drfailov/DRM_Watch_v3/Board/KiCad Project/_DRM_Watch_v3/2023-12-12.jpg

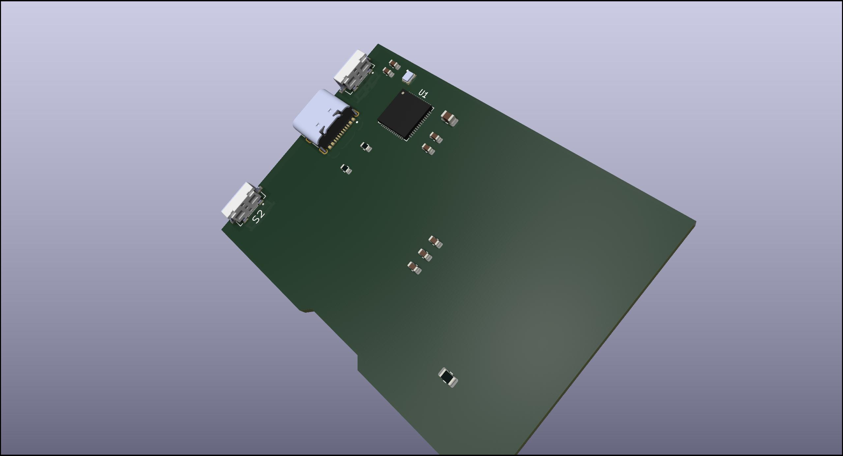
Board/KiCad Project/_DRM_Watch_v3/2023-12-12.jpg
