drfailov/DRM_Watch_v3/Board/KiCad Project/HV816K6 EL Driver/datasheet.png

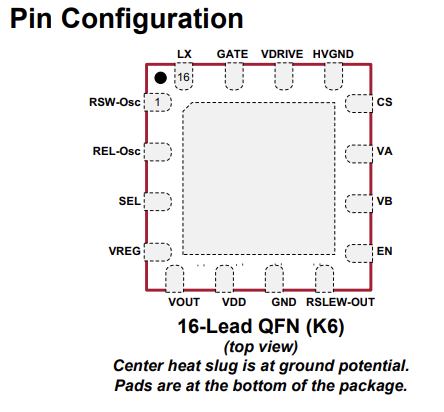
Board/KiCad Project/HV816K6 EL Driver/datasheet.png
