drfailov/DRM_Watch_v3/Board/KiCad Project/HV816K6 EL Driver/footprint.png

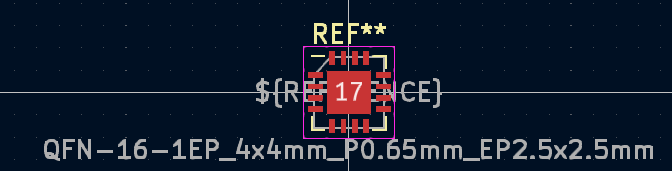
Board/KiCad Project/HV816K6 EL Driver/footprint.png
