drfailov/DRM_Watch_v3/Board/KiCad Project/HV816K6 EL Driver/symbol.png

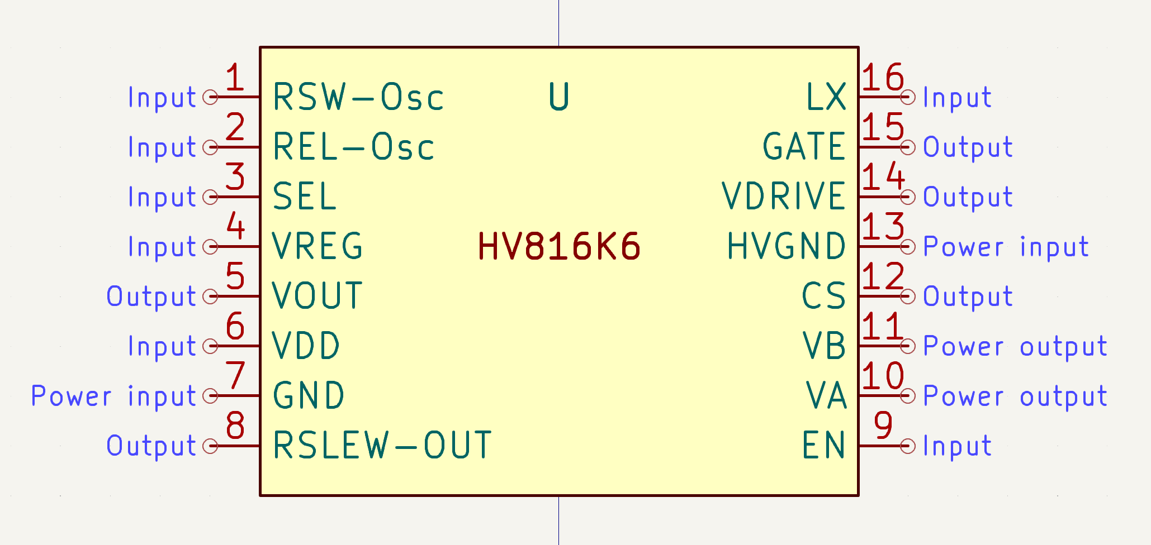
Board/KiCad Project/HV816K6 EL Driver/symbol.png
