drfailov/DRM_Watch_v3/Board/Photos/2023-12-20-1.png

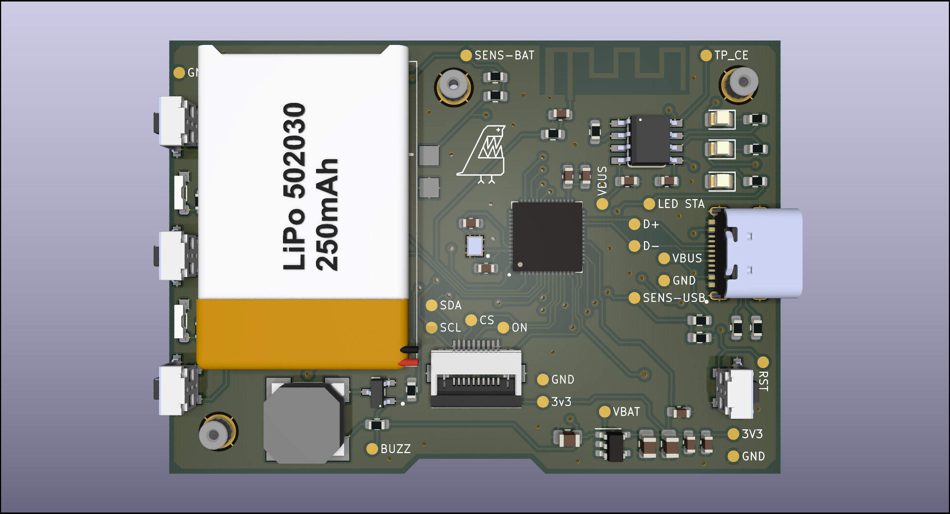
Board/Photos/2023-12-20-1.png
