drfailov/DRM_Watch_v3/Board/Photos/photo_2023-12-13_23-19-55.jpg

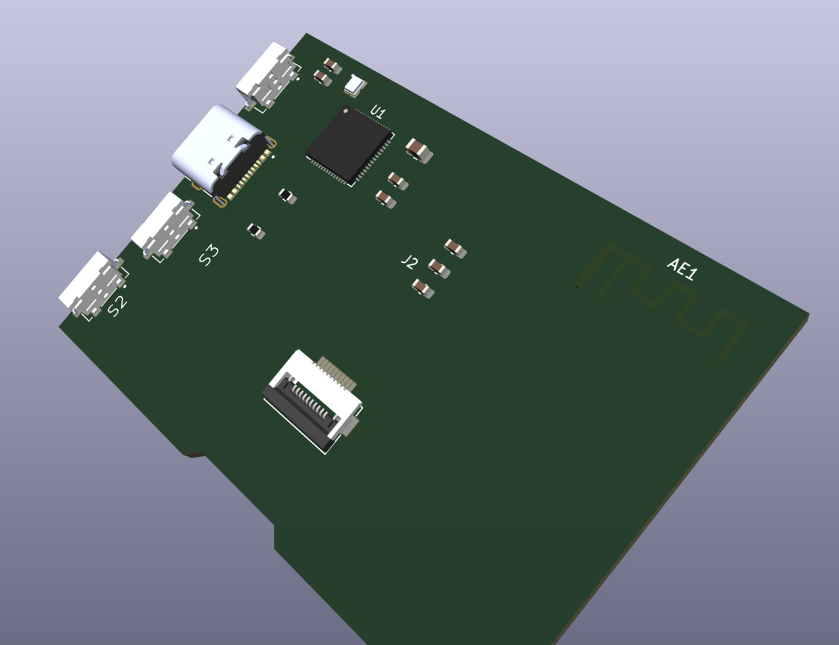
Board/Photos/photo_2023-12-13_23-19-55.jpg
