drfailov/DRM_Watch_v3/Board/Photos/photo_2023-12-15_01-00-38.jpg

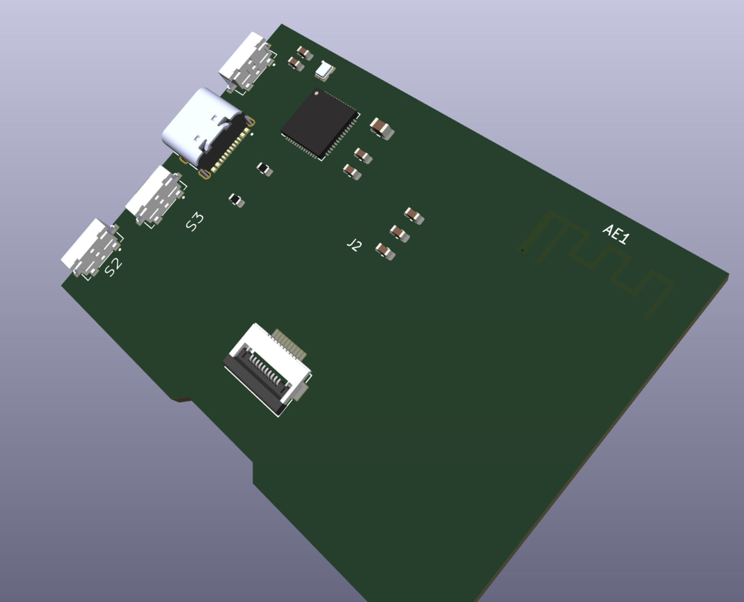
Board/Photos/photo_2023-12-15_01-00-38.jpg
