drfailov/DRM_Watch_v3/Board/Photos/photo_2023-12-16_00-13-19.jpg

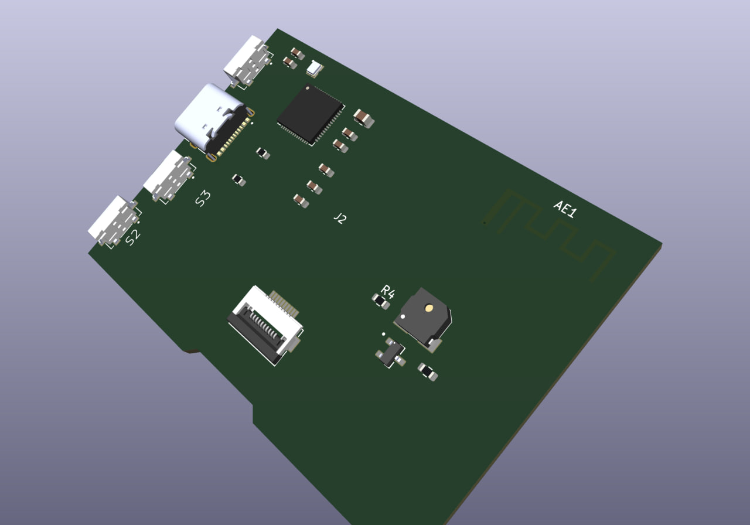
Board/Photos/photo_2023-12-16_00-13-19.jpg
