drfailov/DRM_Watch_v3/Board/Photos/photo_2023-12-16_18-21-03.jpg

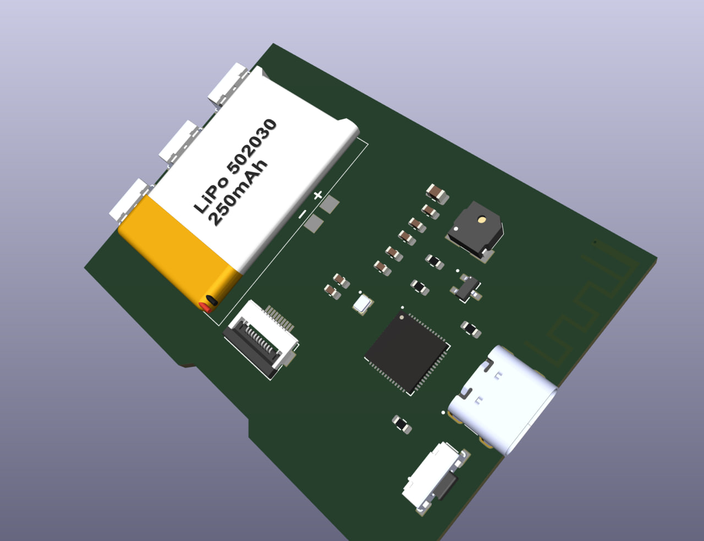
Board/Photos/photo_2023-12-16_18-21-03.jpg
