drfailov/DRM_Watch_v3/Board/Photos/photo_2023-12-16_20-18-11.jpg

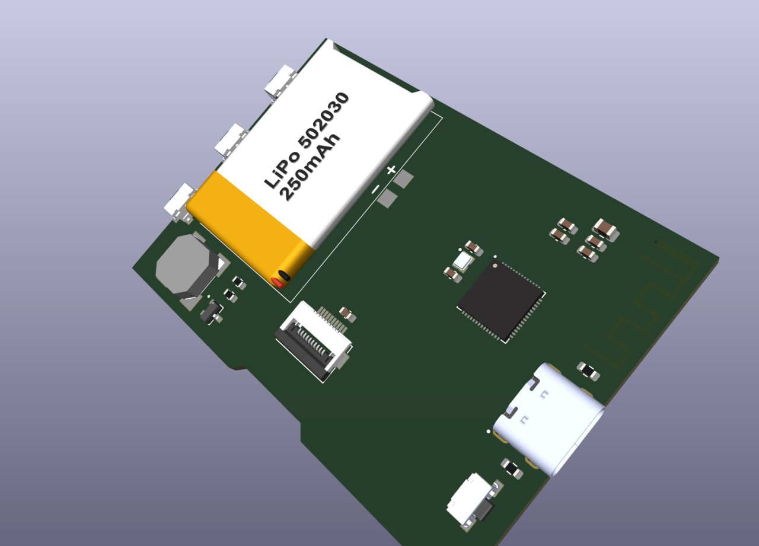
Board/Photos/photo_2023-12-16_20-18-11.jpg
