drfailov/DRM_Watch_v3/Board/Photos/photo_2023-12-17_21-03-23.jpg

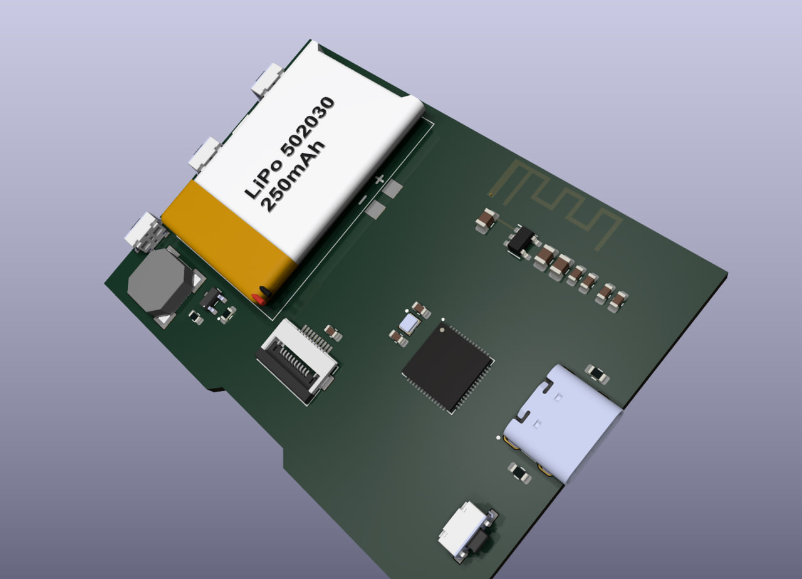
Board/Photos/photo_2023-12-17_21-03-23.jpg
