drfailov/DRM_Watch_v3/Board/Photos/photo_2023-12-18_10-02-20.jpg

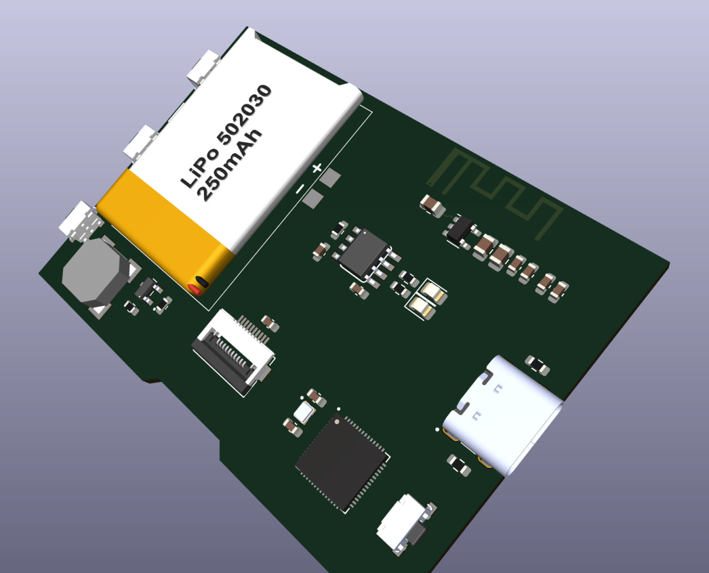
Board/Photos/photo_2023-12-18_10-02-20.jpg
