drfailov/DRM_Watch_v3/Board/Photos/photo_2023-12-18_23-56-38.jpg

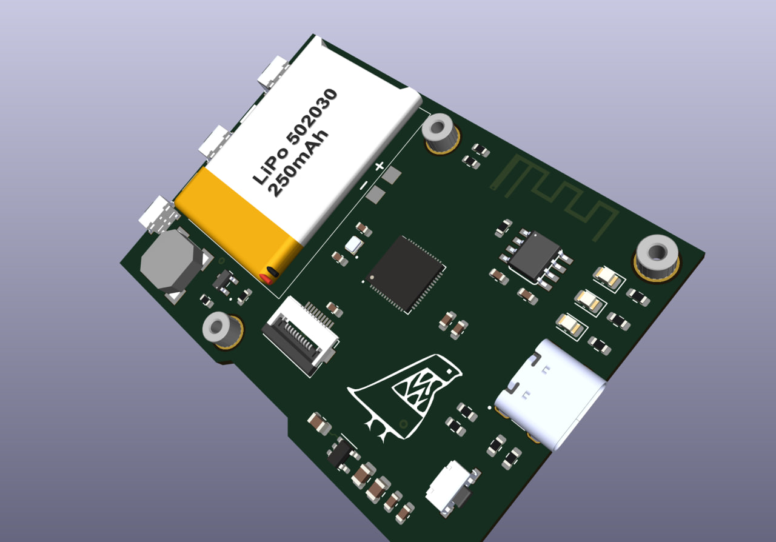
Board/Photos/photo_2023-12-18_23-56-38.jpg
