drfailov/DRM_Watch_v3/Board/Photos/photo_2023-12-20_00-25-11.jpg

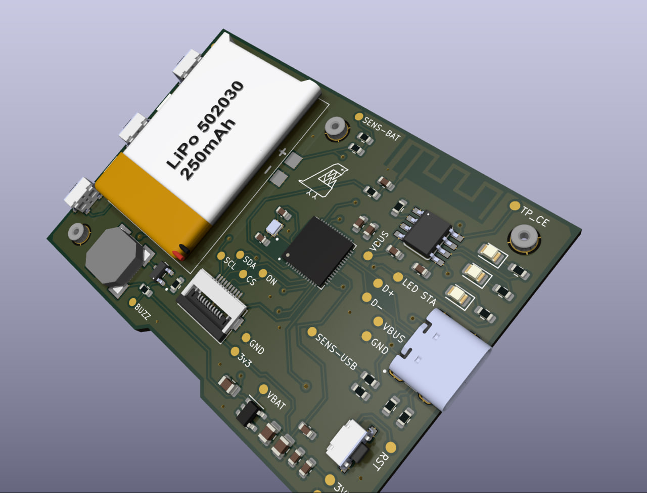
Board/Photos/photo_2023-12-20_00-25-11.jpg
