drfailov/DRM_Watch_v3/Case/2024-04-05 Back Cover Engraving.png

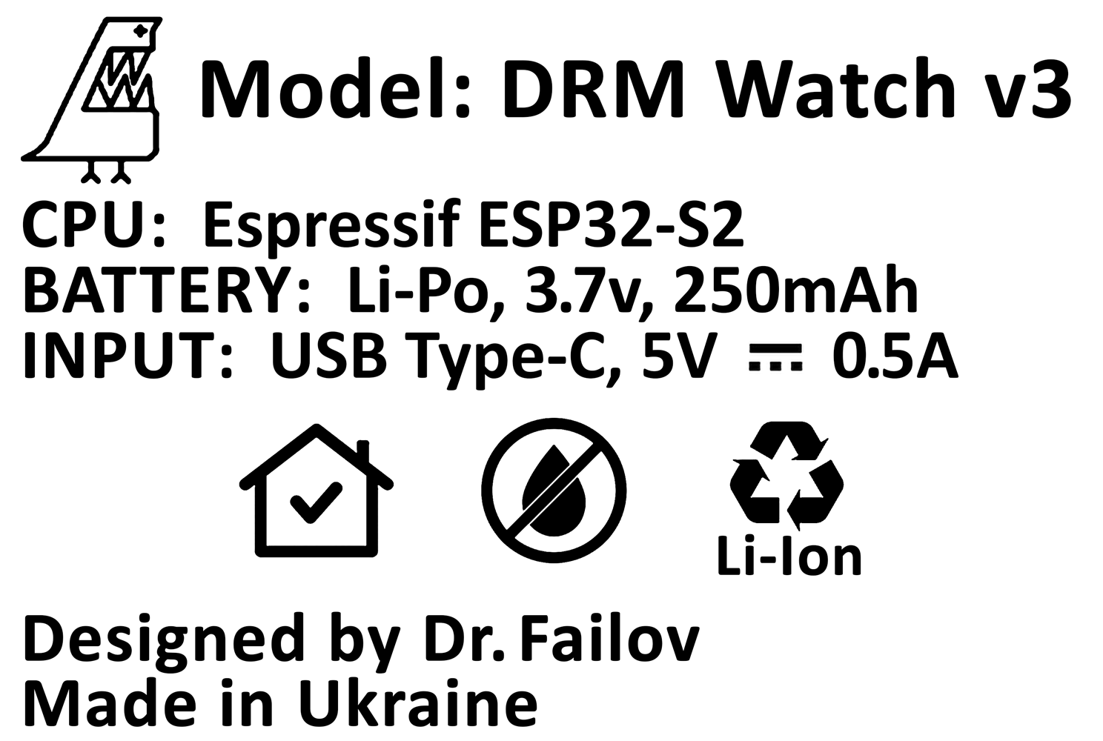
Case/2024-04-05 Back Cover Engraving.png
