drfailov/DRM_Watch_v3/Case/2024-04-16 Front Cover Engraving.png

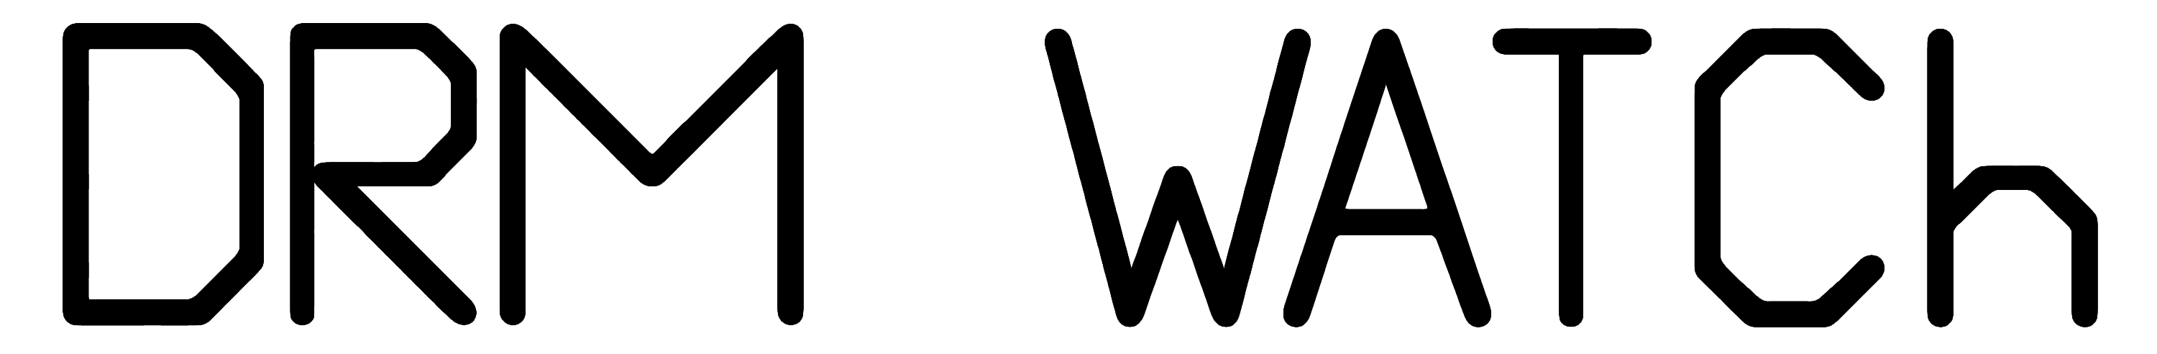
Case/2024-04-16 Front Cover Engraving.png
