drfailov/DRM_Watch_v3/Docs/s2_mini_v1.0.0_4_16x9.jpg

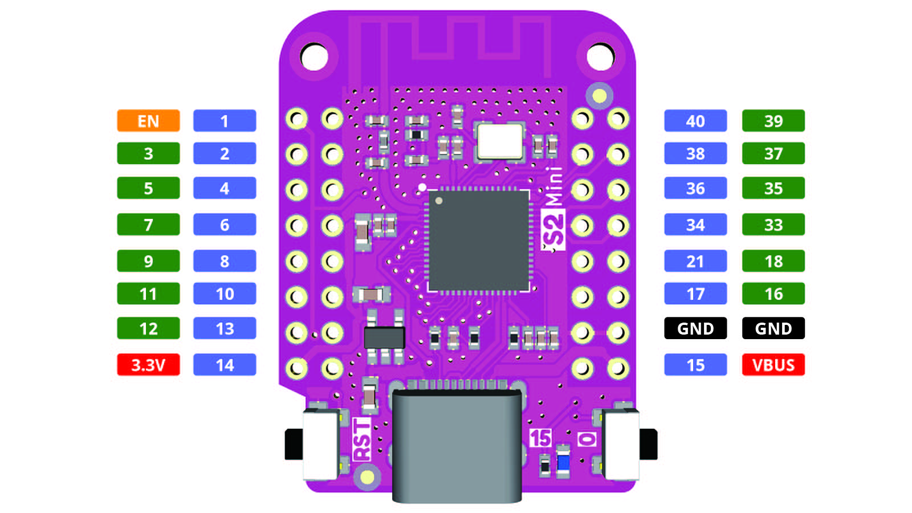
Docs/s2_mini_v1.0.0_4_16x9.jpg
