drfailov/DRM_Watch_v3/Docs/Screenshot 2023-10-04 231237.png

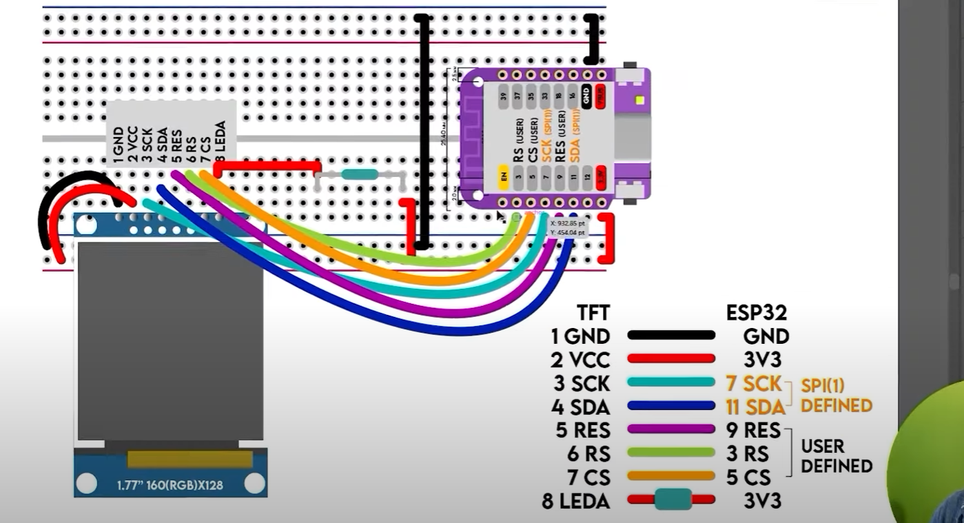
Docs/Screenshot 2023-10-04 231237.png
