drfailov/DRM_Watch_v3/Docs/Screenshot 2024-01-14 173355.png

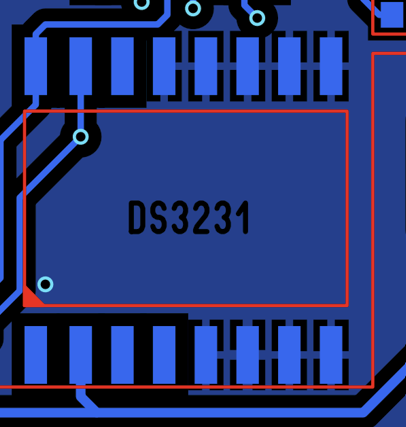
Docs/Screenshot 2024-01-14 173355.png
