drfailov/DRM_Watch_v3/ExampleFiles/capy-Masha.bmp

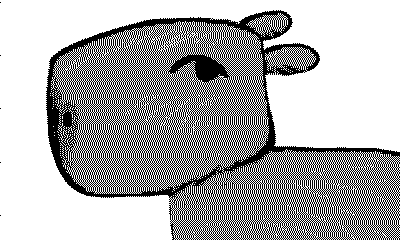
ExampleFiles/capy-Masha.bmp
