drfailov/DRM_Watch_v3/ExampleFiles/capy.bmp

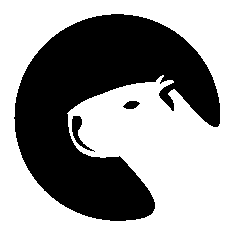
ExampleFiles/capy.bmp
