drfailov/DRM_Watch_v3/ExampleFiles/catGrisha.bmp

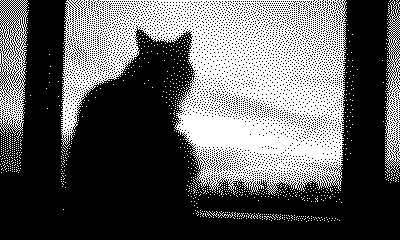
ExampleFiles/catGrisha.bmp
