drfailov/DRM_Watch_v3/ExampleFiles/DRM-Capy-v2.bmp

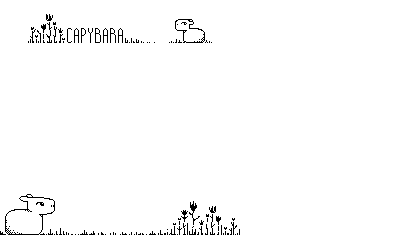
ExampleFiles/DRM-Capy-v2.bmp
