drfailov/DRM_Watch_v3/ExampleFiles/jessy.bmp

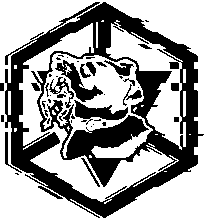
ExampleFiles/jessy.bmp
