drfailov/DRM_Watch_v3/ExampleFiles/mask1.bmp

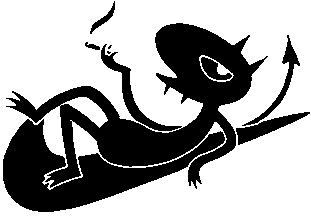
ExampleFiles/mask1.bmp
