drfailov/DRM_Watch_v3/ExampleFiles/mavic.bmp

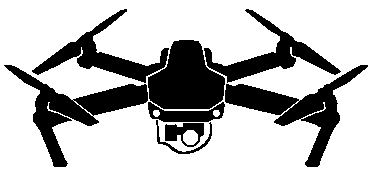
ExampleFiles/mavic.bmp
