drfailov/DRM_Watch_v3/ExampleFiles/Плата.bmp

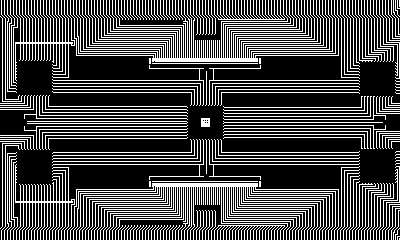
ExampleFiles/Плата.bmp
