drfailov/DRM_Watch_v3/Software/Flasher/esptool-gui/20240626_113028.jpg

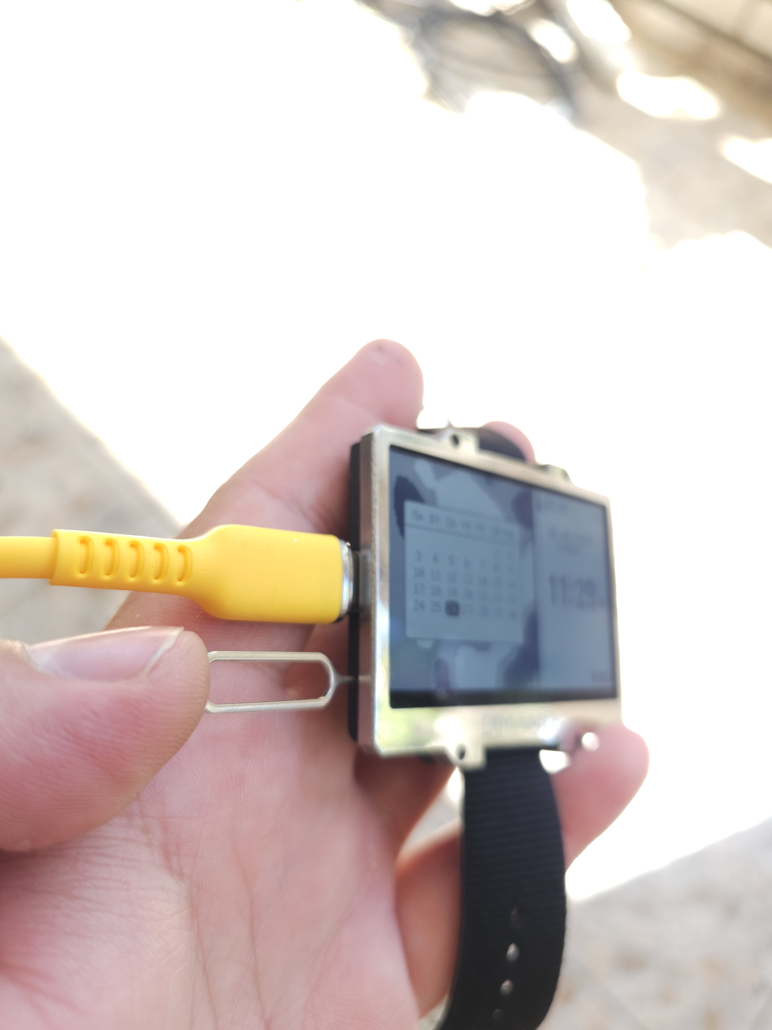
Software/Flasher/esptool-gui/20240626_113028.jpg
