drfailov/DRM_Watch_v3/Software/Flasher/esptool-gui/BootMode.png

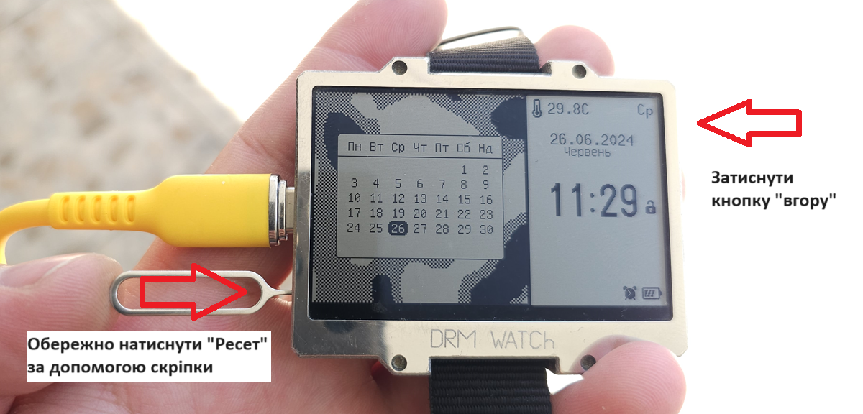
Software/Flasher/esptool-gui/BootMode.png
