drfailov/DRM_Watch_v3/Software/MIDI-to-Arduino-main/preview.jpg

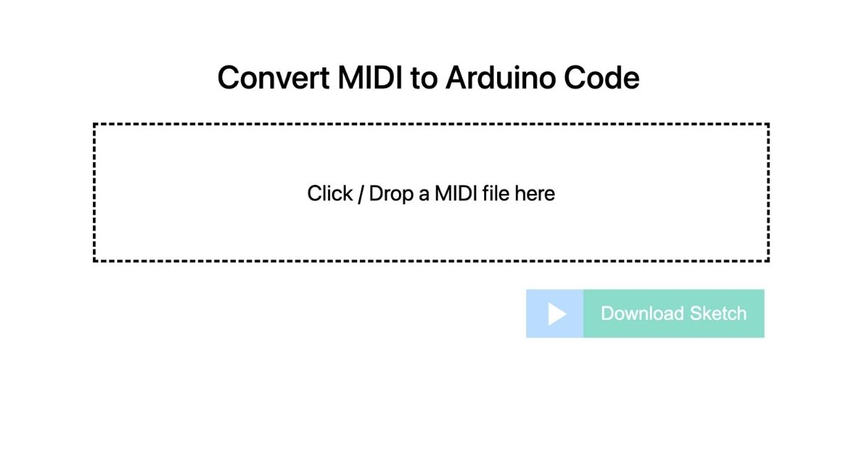
Software/MIDI-to-Arduino-main/preview.jpg
