drfailov/DRM_Watch_v3/Software/ScreenshotTool/loading-314p.gif

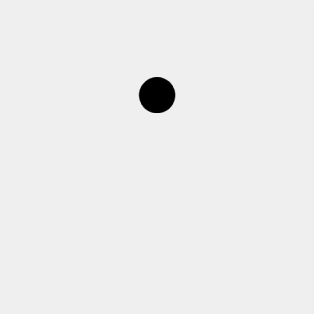
Software/ScreenshotTool/loading-314p.gif
