drfailov/DRM_Watch_v3/Software/ScreenshotTool/screenshot.png

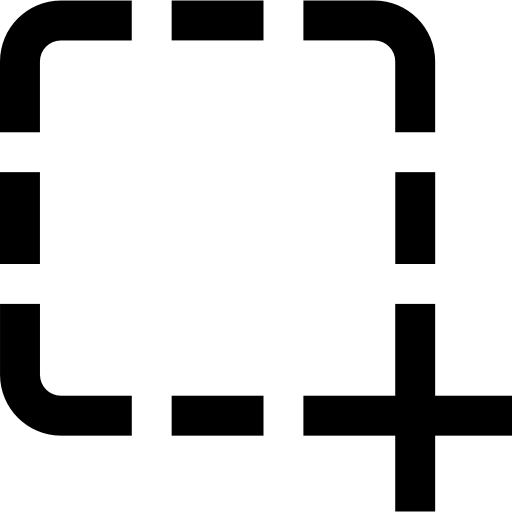
Software/ScreenshotTool/screenshot.png
