drfailov/DRM_Watch_v3/Software/ScreenshotTool/screenshot_tool/Resources/boot-mode-connected.png

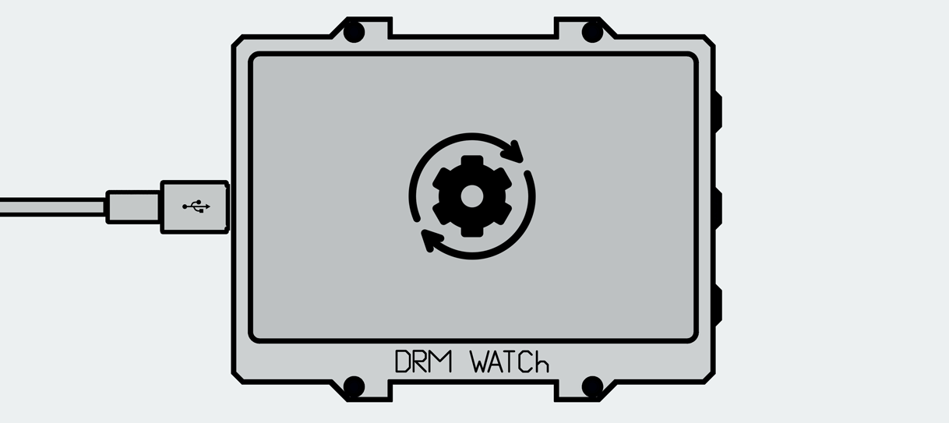
Software/ScreenshotTool/screenshot_tool/Resources/boot-mode-connected.png
