drfailov/DRM_Watch_v3/Case/2024-04-17 v200 front-case-engraving.dxf

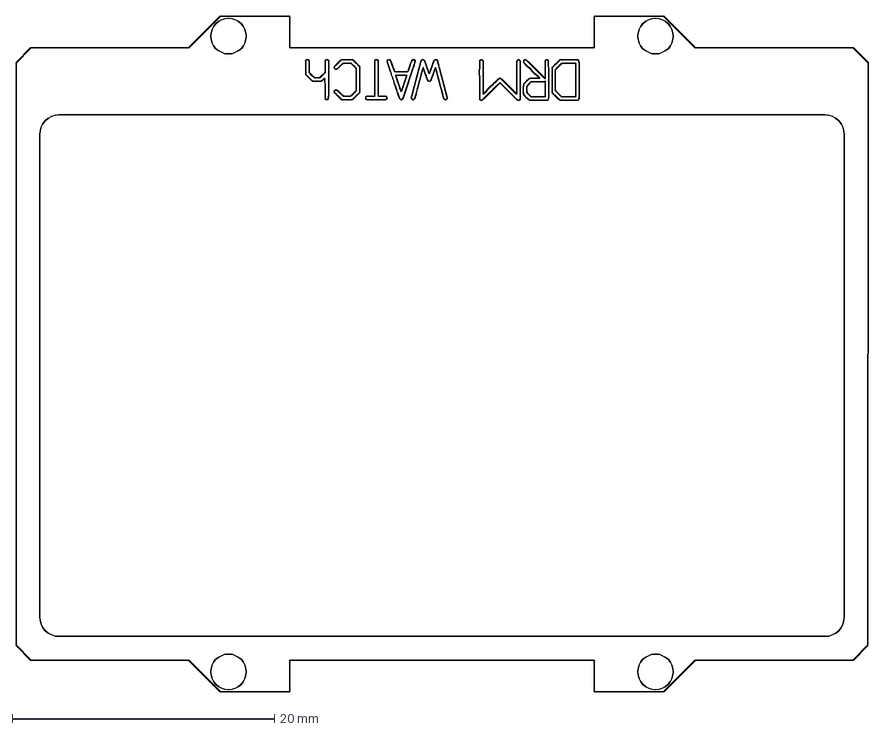
[picture p143: CAD file, 2024-04-18]
Case/2024-04-17 v200 front-case-engraving.dxf
64.9 x 51.4 mm
