drfailov/DRM_Watch_v3/Case/2024-04-17 v200 front-case.step

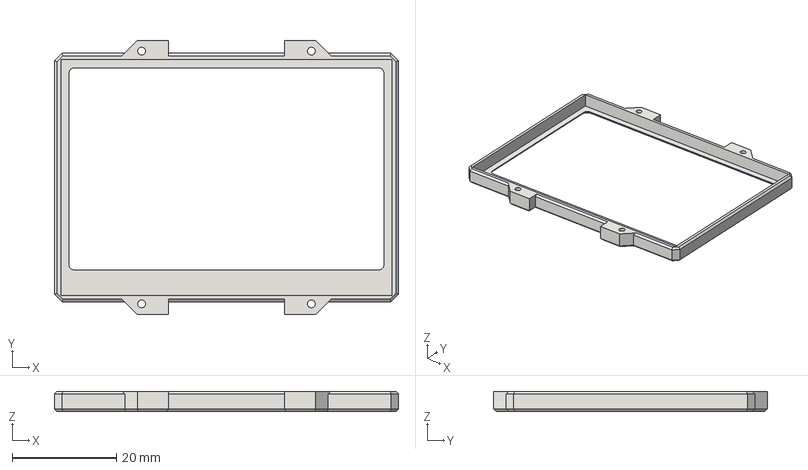
[picture p144: CAD file, 2024-04-18]
Case/2024-04-17 v200 front-case.step
65.9 x 52.4 x 3.90 mm
