drfailov/DRM_Watch_v3/Case/2024-04-17 v200 newbuttons.stl

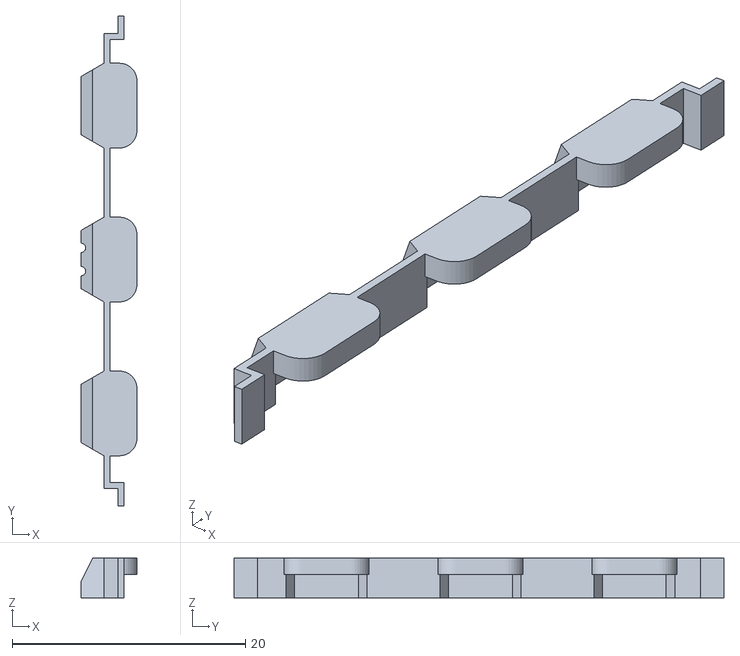
[picture p145: CAD file, 2024-04-17]
Case/2024-04-17 v200 newbuttons.stl
4.80 x 42.0 x 3.40
