drfailov/DRM_Watch_v3/Case/2024-04-05 Back Cover Engraving.dxf

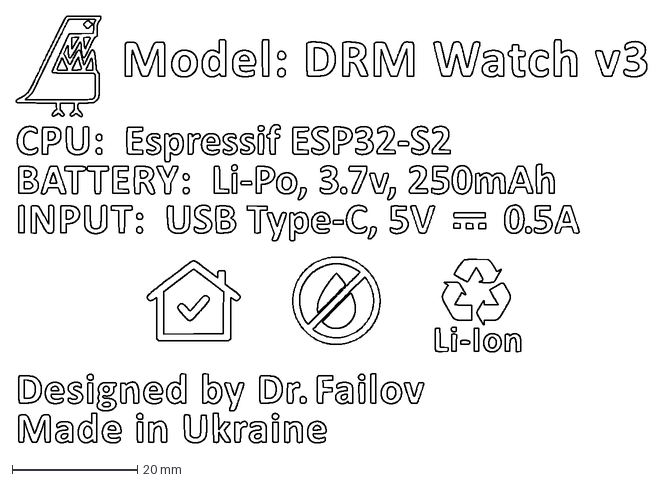
[picture p146: CAD file, 2024-04-06]
Case/2024-04-05 Back Cover Engraving.dxf
100.7 x 68.1 mm
