drfailov/DRM_Watch_v3/Firmware/DRM Watch 3/src/DrmPreferences.h

#ifndef MYYPREFERENCES_H
#define MYYPREFERENCES_H

#define LANG_UA 0
#define LANG_EN 1

/*PROTOTYPES*/
int getPreferencesFreeSpace();
// BATTERY
#define batteryCalibrationLengthMax 100 // 100 is one record for 5 minutes = 8 hours total
int16_t batteryCalibration[batteryCalibrationLengthMax];  //values written from higher[0] battery level to lower[batteryCalibrationLengthMax] battery level. 0 considered as end of data.
bool batteryCalibrationLoaded = false;
float batteryCalibrationGetValuePercent(int raw);
int batteryCalibrationGetIndexOfValue(int raw);
bool isBatteryCalibrated();
int batteryCalibrationLength();
int batteryCalibrationAddValue(int16_t raw);
void batteryCalibrationShrink();
void saveBatteryCalibration();
void resetBatteryCalibration();
void loadBatteryCalibration();
unsigned long getBatteryCalibrationValueAddInterval();
void saveBatteryCalibrationValueAddInterval(unsigned long value);
// SHORTCUTS
int getActionId(int eventId, int defaultActionId);
int getActionId(int eventId);
bool saveActionId(int eventId, int actionId);
int getActionArgument(int eventId);
bool saveActionArgument(int eventId, int value);
String getActionArgumentString(int eventId);
bool saveActionArgumentString(int eventId, String value);
// timer
bool saveTimerStartedTime(unsigned long epoch);
bool saveTimerTime(unsigned long epoch);
unsigned long getTimerStartedTime();
unsigned long getTimerTime();
bool isTimerRunning();
// lcd
bool getInversionValue();
bool getWhiteValue();
bool getBlackValue();
void saveLangValue(int value);
int getLang();
void saveInversionValue(bool value);
void saveEnterAnimationValue(bool value);
bool getEnterAnimationValue();
void saveClearAnimationValue(int value);
int getClearAnimation();
unsigned long getLcdSpiSpeed();
bool saveLcdSpiSpeed(unsigned long spiSpeed);
void saveRoundness(int value);
int getRoundness();
int getRoundness(int max);
// sound
bool getMuteEnabled();
bool saveMuteEnabled(bool value);
int getButtonSound();
bool saveButtonSound(int value);
bool saveSoundCoef(float coef);
float getSoundCoef();
// SAVED WI-FI
int wifiSlotCnt();
String wifiSlotName(int slot);
bool wifiSlotIsEmpty(int slot);
String wifiSlotPassword(int slot);
int getWifiSavedIndex(String name);
bool wifiSlotSave(int slot, String ssid, String password);
bool wifiSlotClear(int slot);
// alert
int getAlertsNumber();
bool getAlertEnabled(int index);
bool saveAlertEnabled(int index, bool value);
bool getAnyAlertEnabled();
int getAlertLastRunDay(int index);
bool saveAlertLastRunDay(int index, int value);
int getAlertHour(int index);
bool saveAlertHour(int index, int value);
int getAlertMinute(int index);
bool saveAlertMinute(int index, int value);
int getAlertMelody(int index);
bool saveAlertMelody(int index, int value);
String getAlertName(int index);
bool saveAlertName(int index, String newname);
// timesync
unsigned long getLastTimeSync();
bool saveLastTimeSync(unsigned long epoch);
bool getTimeSyncEnabled();
bool saveTimeSyncEnabled(bool value);
long getTimeOffsetSec();
bool saveTimeOffsetSec(long value);
bool saveLastChargedTime();
bool saveLastChargedTime(unsigned long epoch);
unsigned long getTimeSinceLastCharged();
unsigned long getLastTryTimeSync();
bool saveLastTryTimeSync(unsigned long epoch);
// stopwatch
bool saveStopwatchStartedTime(unsigned long epoch);
bool saveStopwatchFinishedTime(unsigned long epoch);
unsigned long getStopwatchStartedTime();
unsigned long getStopwatchFinishedTime();
bool isStopwatchRunning();
int stopwatchHistorySlotCnt();
unsigned long stopwatchHistorySlotStart(int slot);
bool stopwatchHistorySlotIsEmpty(int slot);
unsigned long stopwatchHistorySlotEnd(int slot);
bool saveStopwatchHistorySlotStart(int slot, unsigned long epoch);
bool saveStopwatchHistorySlotEnd(int slot, unsigned long epoch);
// watchface
int getWatchface();
bool saveWatchface(int value);
bool getWatchfaceStatusbarEnabled();
bool saveWatchfaceStatusbarEnabled(bool value);
bool getWatchfaceAnalogEnabled();
bool saveWatchfaceAnalogEnabled(bool value);
bool getWatchfaceDigitalEnabled();
bool saveWatchfaceDigitalEnabled(bool value);
bool getWatchfaceStatusbarDigitalEnabled();
bool saveWatchfaceStatusbarDigitalEnabled(bool value);
bool getWatchfaceTemperatureEnabled();
bool saveWatchfaceTemperatureEnabled(bool value);
bool getWatchfaceTemperatureGraphEnabled();
bool saveWatchfaceTemperatureGraphEnabled(bool value);
bool getWatchfaceDayOfWeekEnabled();
bool saveWatchfaceDayOfWeekEnabled(bool value);
bool getWatchfaceDateEnabled();
bool saveWatchfaceDateEnabled(bool value);
bool getWatchfaceMonthEnabled();
bool saveWatchfaceMonthEnabled(bool value);
bool getWatchfaceDjiLogoEnabled();
bool saveWatchfaceDjiLogoEnabled(bool value);
bool getWatchfaceLifeBackgroundEnabled();
bool saveWatchfaceLifeBackgroundEnabled(bool value);
bool getWatchfaceAntBackgroundEnabled();
bool saveWatchfaceAntBackgroundEnabled(bool value);
bool getWatchfaceRandomBackgroundEnabled();
bool saveWatchfaceRandomBackgroundEnabled(bool value);
bool getWatchfaceFireBackgroundEnabled();
bool saveWatchfaceFireBackgroundEnabled(bool value);
bool getWatchfaceLavaBackgroundEnabled();
bool saveWatchfaceLavaBackgroundEnabled(bool value);
bool getWatchfaceDotsBackgroundEnabled();
bool saveWatchfaceDotsBackgroundEnabled(bool value);
bool getWatchfaceCalendarEnabled();
bool saveWatchfaceCalendarEnabled(bool value);
bool getWatchfaceSinceChargedEnabled();
bool saveWatchfaceSinceChargedEnabled(bool value);
bool getWatchfaceFileBackgroundEnable();
bool saveWatchfaceFileBackgroundEnable(bool value);
String getWatchfaceFileBackgroundPath();
bool saveWatchfaceFileBackgroundPath(String path);
// ant
int getAntSpeed();
bool saveAntSpeed(int value);

#include <Preferences.h>
#include "Buzzer.h"
#include "ModeWatchface.h"
#include "Rtc.h"

//   max name len: 15

Preferences preferencesObject;

void initPreferences()
{
  preferencesObject.begin("drm-watch-v3", false);
}

//----------------------//---------------------- BATTERY ----------//----------------------//----------------------//----------------------//----------------------
void loadBatteryCalibration()  //load from preferences patrition
{
  if (preferencesObject.isKey("batteryCali"))
  {
    preferencesObject.getBytes("batteryCali", &batteryCalibration, sizeof(batteryCalibration));
  }
  else
  {
    for (int i = 0; i < batteryCalibrationLengthMax; i++)
      batteryCalibration[i] = 0;
  }
  batteryCalibrationLoaded = true;
}
void saveBatteryCalibration()  //save to preferences patrition
{
  if(!batteryCalibrationLoaded)
    loadBatteryCalibration();
  preferencesObject.putBytes("batteryCali", (byte *)(&batteryCalibration), sizeof(batteryCalibration));
}
void resetBatteryCalibration()
{
  if(!batteryCalibrationLoaded)
    loadBatteryCalibration();
  for (int i = 0; i < batteryCalibrationLengthMax; i++)
      batteryCalibration[i] = 0;
  saveBatteryCalibration();    
}
bool isBatteryCalibrated()
{
  if(!batteryCalibrationLoaded)
    loadBatteryCalibration();
  return batteryCalibration[0] > 0 && batteryCalibration[0] <= 8192;
}
void batteryCalibrationShrink()
{
  if(!batteryCalibrationLoaded)
    loadBatteryCalibration();
  int length = batteryCalibrationLength();
  for (int i = 0; i < batteryCalibrationLengthMax; i++)
  {
    int src = i*2;
    if(src < batteryCalibrationLength())
      batteryCalibration[i] = batteryCalibration[src];
    else
      batteryCalibration[i] = 0;
  }
  saveBatteryCalibration();
}
int batteryCalibrationAddValue(int16_t raw) //add to end. Returns current length
{
  int length = batteryCalibrationLength();
  if(length < batteryCalibrationLengthMax){
    batteryCalibration[length] = raw;
    Serial.print("Added raw ");
    Serial.print(raw);
    Serial.print(" to index ");
    Serial.println(length);
    saveBatteryCalibration();
    length ++;
  }
  return length;
} 
int batteryCalibrationLength()  //how many values actually filled
{
  if(!batteryCalibrationLoaded)
    loadBatteryCalibration();
  for (int i = 0; i < batteryCalibrationLengthMax; i++)
  {
    if (batteryCalibration[i] == 0)
      return i;
  }
  return batteryCalibrationLengthMax;
}
int batteryCalibrationGetIndexOfValue(int raw) //on which index is located given value (0 ... batteryCalibrationLengthMax)
{
  if(!batteryCalibrationLoaded)
    loadBatteryCalibration();
  if(raw <= 0 || raw > 8096)
    return 0;
  if(!isBatteryCalibrated())
    return 0;
  if(raw > batteryCalibration[0])
    return 0;
  for (int i = 0; i < batteryCalibrationLengthMax-1; i++)
  {
    int cur = batteryCalibration[i];
    int next = batteryCalibration[i+1];
    if(cur==0 || next==0)  //end of array
      return i;
    if (min(cur, next)<=raw && max(cur, next)>raw)
      return i;
  }
  return batteryCalibrationLengthMax;
}
float batteryCalibrationGetValuePercent(int raw) //which persent of charge (0...100) is this RAW value (0...4096)
{
  if(!isBatteryCalibrated())
    return -1;
  float total = batteryCalibrationLength();
  float curr = batteryCalibrationGetIndexOfValue(raw);   //0=100; total=0
  return map(curr, 0, total, 100/*%*/, 0/*%*/);
}
unsigned long getBatteryCalibrationValueAddInterval()
{                                  //1234567890123
  return preferencesObject.getULong("batCaliInte", 1000*5); //defailt is 5s
}
void saveBatteryCalibrationValueAddInterval(unsigned long value)
{
  preferencesObject.putULong("batCaliInte", value);
}

//----------------------//---------------------- SHORTCUTS ----------//----------------------//----------------------//----------------------//----------------------
int getActionId(int eventId, int defaultActionId)
{ // 123456789012345
  return preferencesObject.getInt((String("action") + eventId).c_str(), defaultActionId);
}
int getActionId(int eventId)
{ // 123456789012345
  int defaultActionId = defaultAction(eventId);
  return preferencesObject.getInt((String("action") + eventId).c_str(), defaultActionId);
}
bool saveActionId(int eventId, int actionId)
{
  return preferencesObject.putInt((String("action") + eventId).c_str(), actionId);
}

int getActionArgument(int eventId)
{ // 123456789012345
  return preferencesObject.getInt((String("actArg") + eventId).c_str(), 0);
}
bool saveActionArgument(int eventId, int value)
{
  return preferencesObject.putInt((String("actArg") + eventId).c_str(), value);
}
String getActionArgumentString(int eventId)
{
  return preferencesObject.getString((String("actArgStr") + eventId).c_str(), "");
}
bool saveActionArgumentString(int eventId, String value)
{
  return preferencesObject.putString((String("actArgStr") + eventId).c_str(), value);
}

//----------------------//---------------------- TIMER ----------//----------------------//----------------------//----------------------//----------------------

bool saveTimerStartedTime(unsigned long epoch)
{ // unsigned long    saveTimerStartedTime  saveTimerTime  getTimerStartedTime  getTimerTime  isTimerRunning
  return preferencesObject.putULong64("timerSta", epoch) > 0;
}

bool saveTimerTime(unsigned long epoch)
{
  return preferencesObject.putULong64("timerTime", epoch) > 0;
}

unsigned long getTimerStartedTime()
{
  return preferencesObject.getULong64("timerSta", 0);
}

unsigned long getTimerTime()
{
  return preferencesObject.getULong64("timerTime", 0);
}

bool isTimerRunning()
{
  return getTimerStartedTime() != 0;
}

//----------------------//---------------------- STOPWATCH ----------//----------------------//----------------------//----------------------//----------------------

bool saveStopwatchStartedTime(unsigned long epoch)
{
  return preferencesObject.putULong64("stopwatch1", epoch) > 0;
}

bool saveStopwatchFinishedTime(unsigned long epoch)
{
  return preferencesObject.putULong64("stopwatch2", epoch) > 0;
}

unsigned long getStopwatchStartedTime()
{
  return preferencesObject.getULong64("stopwatch1", 0);
}

unsigned long getStopwatchFinishedTime()
{
  return preferencesObject.getULong64("stopwatch2", 0);
}

bool isStopwatchRunning()
{
  return getStopwatchStartedTime() != 0 && getStopwatchFinishedTime() == 0;
}

int stopwatchHistorySlotCnt()
{
  return 5;
}

unsigned long stopwatchHistorySlotStart(int slot)
{ // 1 ... stopwatchHistorySlotCnt
  return preferencesObject.getULong64((String("sws") + slot + "sta").c_str(), 0);
}
bool stopwatchHistorySlotIsEmpty(int slot)
{ // 1 ... stopwatchHistorySlotCnt
  return stopwatchHistorySlotStart(slot) == 0;
}

unsigned long stopwatchHistorySlotEnd(int slot)
{ // 1 ... stopwatchHistorySlotCnt
  return preferencesObject.getULong64((String("sws") + slot + "end").c_str(), 0);
}

bool saveStopwatchHistorySlotStart(int slot, unsigned long epoch)
{ // 1 ... stopwatchHistorySlotCnt
  return preferencesObject.putULong64((String("sws") + slot + "sta").c_str(), epoch) > 0;
}

bool saveStopwatchHistorySlotEnd(int slot, unsigned long epoch)
{ // 1 ... stopwatchHistorySlotCnt
  return preferencesObject.putULong64((String("sws") + slot + "end").c_str(), epoch) > 0;
}

//----------------------//---------------------- SAVED WI-FI --------//----------------------//----------------------//----------------------//----------------------

int wifiSlotCnt()
{
  return 7;
}

String wifiSlotName(int slot)
{ // 1 ... wifiSlotCnt
  return preferencesObject.getString((String("ws") + slot + "n").c_str(), "-empty-");
}

bool wifiSlotIsEmpty(int slot)
{ // 1 ... wifiSlotCnt
  return wifiSlotName(slot).equals("-empty-");
}

String wifiSlotPassword(int slot)
{ // 1 ... wifiSlotCnt
  return preferencesObject.getString((String("ws") + slot + "p").c_str(), "-empty-");
}

int getWifiSavedIndex(String name)
{
  for (int i = 1; i < wifiSlotCnt(); i++)
  {
    if (wifiSlotName(i) == name)
      return i;
  }
  return -1;
}

bool wifiSlotSave(int slot, String ssid, String password)
{ // 1 ... wifiSlotCnt
  int savedSsid = preferencesObject.putString((String("ws") + slot + "n").c_str(), ssid);
  int savedPassword = preferencesObject.putString((String("ws") + slot + "p").c_str(), password);
  return savedSsid > 0 && savedPassword > 0;
}

bool wifiSlotClear(int slot)
{ // 1 ... wifiSlotCnt
  return wifiSlotSave(slot, "-empty-", "-empty-");
}

//----------------------//---------------------- TIMEZONE ------------//----------------------//----------------------//----------------------//----------------------

long getTimeOffsetSec()
{ // 123456789012345
  return preferencesObject.getInt("timeOffsetSec", 60 * 60 * 2);
}
bool saveTimeOffsetSec(long value)
{
  return preferencesObject.putInt("timeOffsetSec", value);
}

//----------------------//---------------------- TIME SYNC ------------//----------------------//----------------------//----------------------//----------------------
bool getTimeSyncEnabled()
{ // 123456789012345
  return preferencesObject.getInt((String("TimeSyncEnable")).c_str(), 0) == 1;
}
bool saveTimeSyncEnabled(bool value)
{
  return preferencesObject.putInt((String("TimeSyncEnable")).c_str(), value ? 1 : 0);
}
bool saveLastTryTimeSync(unsigned long epoch)
{
  return preferencesObject.putULong64("lastTryTimeSync", epoch) > 0;
}
unsigned long getLastTryTimeSync()
{
  return preferencesObject.getULong64("lastTryTimeSync", 0);
}
bool saveLastTimeSync(unsigned long epoch)
{
  return preferencesObject.putULong64("lastTimeSync1", epoch) > 0;
}
unsigned long getLastTimeSync()
{
  return preferencesObject.getULong64("lastTimeSync1", 0);
}
// bool saveTimeCoef(double coef){
//   return preferencesObject.putDouble("timeCorrection1", coef) > 0;
// }
// double getTimeCoef(){
//   return preferencesObject.getDouble("timeCorrection1", 0);
// }

//----------------------//---------------------- DISPLAY -------//----------------------//----------------------//----------------------//----------------------

bool getInversionValue()
{
  return preferencesObject.getInt("screenInverse", 0) == 1;
}
bool getWhiteValue()
{
  return !getInversionValue();
}
bool getBlackValue()
{
  return getInversionValue();
}
void saveInversionValue(bool value)
{
  preferencesObject.putInt("screenInverse", value ? 1 : 0);
}
int langCache = -1;
void saveLangValue(int value)
{
  langCache = value;
  preferencesObject.putInt("lang", langCache);
}
int getLang()
{
  if (langCache == -1)
    langCache = preferencesObject.getInt("lang", LANG_UA);
  return langCache;
}
bool getEnterAnimationValue()
{
  return preferencesObject.getInt("screenInAnim", 1) == 1;
}
void saveEnterAnimationValue(bool value)
{
  preferencesObject.putInt("screenInAnim", value ? 1 : 0);
}
void saveClearAnimationValue(int value)
{
  preferencesObject.putInt("screenOutAnim", value);
}
int getClearAnimation()
{
  return preferencesObject.getInt("screenOutAnim", 3);
}
unsigned long getLcdSpiSpeed()
{
  return preferencesObject.getULong64("spiSpeed", 2000000); // 1MHz is default, 2MHz is max recommended, 3.5MHz is still OK, 4MHz is glitchy, 5MHZ not working at all
}
bool saveLcdSpiSpeed(unsigned long spiSpeed)
{
  return preferencesObject.putULong64("spiSpeed", spiSpeed) > 0;
}
int roundnessCache = -1;
void saveRoundness(int value)
{
  roundnessCache = value;
  preferencesObject.putInt("roundness", roundnessCache);
}
int getRoundness()
{ 
  if(roundnessCache < 0)
    roundnessCache = preferencesObject.getInt("roundness", 4);
  if(roundnessCache > 19) 
    roundnessCache = 19;
  if(roundnessCache < 0) 
    roundnessCache = 0;
  return roundnessCache;
}
int getRoundness(int max)
{
  int r = getRoundness();
  if(r>max)
    return max;
  return r;
}


//----------------------//---------------------- LAST CHARGED ------------//----------------------//----------------------//----------------------//----------------------

unsigned long getLastChargedTime()
{
  return preferencesObject.getULong64("LastCharged", 0);
}
unsigned long getTimeSinceLastCharged()
{
  return rtcGetEpoch() - getLastChargedTime();
}
bool saveLastChargedTime(unsigned long epoch)
{
  return preferencesObject.putULong64("LastCharged", epoch) > 0;
}
bool saveLastChargedTime()
{
  return saveLastChargedTime(rtcGetEpoch());
}

//----------------------//---------------------- SOUND -----------------//----------------------//----------------------//----------------------//----------------------

bool getMuteEnabled()
{ // 123456789012345
  return preferencesObject.getInt((String("soundMute")).c_str(), 0) == 1;
}
bool saveMuteEnabled(bool value)
{
  return preferencesObject.putInt((String("soundMute")).c_str(), value ? 1 : 0);
}

int getButtonSound()
{
  return preferencesObject.getInt("ButtonSound", 1);
}
bool saveButtonSound(int value)
{
  int totalSounds = buttonBeepCnt();
  return preferencesObject.putInt("ButtonSound", value % totalSounds);
}

float soundCoefCache = -1;
bool saveSoundCoef(float coef)
{
  soundCoefCache = coef;
  return preferencesObject.putFloat("soundCoef", coef) > 0;
}
float getSoundCoef()
{
  if (soundCoefCache == -1)
    soundCoefCache = preferencesObject.getFloat("soundCoef", 1.0);
  return soundCoefCache;
}

//----------------------//---------------------- ANT SPEED -----------------//----------------------//----------------------//----------------------//----------------------

int getAntSpeed()
{ // getAntSpeed   saveAntSpeed
  return preferencesObject.getInt("AntSpeed", 50);
}
bool saveAntSpeed(int value)
{
  return preferencesObject.putInt("AntSpeed", value);
}

//----------------------//---------------------- WATCHFACE -----------------//----------------------//----------------------//----------------------//----------------------

int getWatchface()
{
  return preferencesObject.getInt("Watchface", 0);
}
bool saveWatchface(int value)
{
  int total = getWatchfaceCount();
  return preferencesObject.putInt("Watchface", value % total);
}
bool getWatchfaceStatusbarEnabled()
{ // 123456789012345   max length = 15
  return preferencesObject.getInt("wtfStatusbarEn", 1) == 1;
}
bool saveWatchfaceStatusbarEnabled(bool value)
{
  return preferencesObject.putInt("wtfStatusbarEn", value ? 1 : 0);
}
bool getWatchfaceAnalogEnabled()
{ // 123456789012345   max length = 15
  return preferencesObject.getInt("wtfAnalogEn", 0) == 1;
}
bool saveWatchfaceAnalogEnabled(bool value)
{
  return preferencesObject.putInt("wtfAnalogEn", value ? 1 : 0);
}
bool getWatchfaceDigitalEnabled()
{ // 123456789012345   max length = 15
  return preferencesObject.getInt("wtfDigitalEn", 1) == 1;
}
bool saveWatchfaceDigitalEnabled(bool value)
{
  return preferencesObject.putInt("wtfDigitalEn", value ? 1 : 0);
}
bool getWatchfaceStatusbarDigitalEnabled()
{ // 123456789012345   max length = 15
  return preferencesObject.getInt("wtfStDigitalEn", 0) == 1;
}
bool saveWatchfaceStatusbarDigitalEnabled(bool value)
{
  return preferencesObject.putInt("wtfStDigitalEn", value ? 1 : 0);
}
bool getWatchfaceTemperatureEnabled()
{ // 123456789012345   max length = 15
  return preferencesObject.getInt("wtfTempEn", 1) == 1;
}
bool saveWatchfaceTemperatureEnabled(bool value)
{
  return preferencesObject.putInt("wtfTempEn", value ? 1 : 0);
}
bool getWatchfaceTemperatureGraphEnabled()
{ // 123456789012345   max length = 15
  return preferencesObject.getInt("wtfTempGrEn", 0) == 1;
}
bool saveWatchfaceTemperatureGraphEnabled(bool value)
{
  return preferencesObject.putInt("wtfTempGrEn", value ? 1 : 0);
}
bool getWatchfaceDayOfWeekEnabled()
{ // 123456789012345   max length = 15
  return preferencesObject.getInt("wtfDayOfWeekEn", 1) == 1;
}
bool saveWatchfaceDayOfWeekEnabled(bool value)
{
  return preferencesObject.putInt("wtfDayOfWeekEn", value ? 1 : 0);
}
bool getWatchfaceDateEnabled()
{ // 123456789012345   max length = 15
  return preferencesObject.getInt("wtfDateEn", 1) == 1;
}
bool saveWatchfaceDateEnabled(bool value)
{
  return preferencesObject.putInt("wtfDateEn", value ? 1 : 0);
}
bool getWatchfaceMonthEnabled()
{ // 123456789012345   max length = 15
  return preferencesObject.getInt("wtfMonthEn", 1) == 1;
}
bool saveWatchfaceMonthEnabled(bool value)
{
  return preferencesObject.putInt("wtfMonthEn", value ? 1 : 0);
}
bool getWatchfaceDjiLogoEnabled()
{ // 123456789012345   max length = 15
  return preferencesObject.getInt("wtfDjiEn", 0) == 1;
}
bool saveWatchfaceDjiLogoEnabled(bool value)
{
  return preferencesObject.putInt("wtfDjiEn", value ? 1 : 0);
}
bool getWatchfaceLifeBackgroundEnabled()
{ // 123456789012345   max length = 15
  return preferencesObject.getInt("wtfLifeEn", 0) == 1;
}
bool saveWatchfaceLifeBackgroundEnabled(bool value)
{
  return preferencesObject.putInt("wtfLifeEn", value ? 1 : 0);
}
bool getWatchfaceAntBackgroundEnabled()
{ // 123456789012345   max length = 15
  return preferencesObject.getInt("wtfAntEn", 0) == 1;
}
bool saveWatchfaceAntBackgroundEnabled(bool value)
{
  return preferencesObject.putInt("wtfAntEn", value ? 1 : 0);
}
bool getWatchfaceRandomBackgroundEnabled()
{ // 123456789012345   max length = 15
  return preferencesObject.getInt("wtfRndEn", 0) == 1;
}
bool saveWatchfaceRandomBackgroundEnabled(bool value)
{
  return preferencesObject.putInt("wtfRndEn", value ? 1 : 0);
}
bool getWatchfaceFireBackgroundEnabled()
{ // 123456789012345   max length = 15
  return preferencesObject.getInt("wtfFireEn", 1) == 1;
}
bool saveWatchfaceFireBackgroundEnabled(bool value)
{
  return preferencesObject.putInt("wtfFireEn", value ? 1 : 0);
}
bool getWatchfaceLavaBackgroundEnabled()
{ // 123456789012345   max length = 15
  return preferencesObject.getInt("wtfLavaEn", 0) == 1;
}
bool saveWatchfaceLavaBackgroundEnabled(bool value)
{
  return preferencesObject.putInt("wtfLavaEn", value ? 1 : 0);
}
bool getWatchfaceDotsBackgroundEnabled()
{ // 123456789012345   max length = 15
  return preferencesObject.getInt("wtfDotEn", 0) == 1;
}
bool saveWatchfaceDotsBackgroundEnabled(bool value)
{
  return preferencesObject.putInt("wtfDotEn", value ? 1 : 0);
}
bool getWatchfaceCalendarEnabled()
{ // 123456789012345   max length = 15
  return preferencesObject.getInt("wtfCalendarEn", 1) == 1;
}
bool saveWatchfaceCalendarEnabled(bool value)
{
  return preferencesObject.putInt("wtfCalendarEn", value ? 1 : 0);
}
bool getWatchfaceSinceChargedEnabled()
{ // 123456789012345   max length = 15
  return preferencesObject.getInt("wtfSCEn", 0) == 1;
}
bool saveWatchfaceSinceChargedEnabled(bool value)
{
  return preferencesObject.putInt("wtfSCEn", value ? 1 : 0);
}
bool getWatchfaceFileBackgroundEnable()
{                               // 123456789012345   max length = 15
  return preferencesObject.getInt("wtfBgFileEn", 0) == 1;
}
bool saveWatchfaceFileBackgroundEnable(bool value)
{
  return preferencesObject.putInt("wtfBgFileEn", value ? 1 : 0);
}
String getWatchfaceFileBackgroundPath()
{                                  // 123456789012345   max length = 15
  return preferencesObject.getString("wtfBgFilePath", "");
}
bool saveWatchfaceFileBackgroundPath(String path)
{
  return preferencesObject.putString("wtfBgFilePath", path);
}

//----------------------//---------------------- ALERT -----------------//----------------------//----------------------//----------------------//----------------------
/*  bool alertIsEnabled = eepromReadAlertEnabled();
    byte alertLastRunDay = eepromReadAlertLastDayRun();
    byte alertTimeHour = eepromReadAlertHour();
    byte alertTimeMinute = eepromReadAlertMinute();
    byte alertMelodyIndex = eepromReadAlertMelodyIndex();*/

int getAlertsNumber()
{
  return 10;
}
bool getAlertEnabled(int index)
{ // 123456789012345
  return preferencesObject.getInt((String("alertEnabled") + index).c_str(), 0) == 1;
}
bool saveAlertEnabled(int index, bool value)
{
  return preferencesObject.putInt((String("alertEnabled") + index).c_str(), value ? 1 : 0);
}
int getAlertLastRunDay(int index)
{ // 123456789012345
  return preferencesObject.getInt((String("alertLRD") + index).c_str(), 0);
}
bool saveAlertLastRunDay(int index, int value)
{
  return preferencesObject.putInt((String("alertLRD") + index).c_str(), value);
}
int getAlertHour(int index)
{ // 123456789012345
  return preferencesObject.getInt((String("alertHour") + index).c_str(), 0);
}
bool saveAlertHour(int index, int value)
{
  return preferencesObject.putInt((String("alertHour") + index).c_str(), value);
}
int getAlertMinute(int index)
{ // 123456789012345
  return preferencesObject.getInt((String("alertMinute") + index).c_str(), 0);
}
bool saveAlertMinute(int index, int value)
{
  return preferencesObject.putInt((String("alertMinute") + index).c_str(), value);
}
int getAlertMelody(int index)
{ // 123456789012345
  return preferencesObject.getInt((String("alertMelody") + index).c_str(), 0);
}
bool saveAlertMelody(int index, int value)
{
  return preferencesObject.putInt((String("alertMelody") + index).c_str(), value);
}
String getAlertName(int index)
{
  return preferencesObject.getString((String("alert") + index + "Name").c_str(), (String("Alert ") + index));
}
bool saveAlertName(int index, String newname)
{
  int savedName = preferencesObject.putString((String("alert") + index + "Name").c_str(), newname);
  return savedName > 0;
}

//----------------------//----------------------//----------------------//----------------------//----------------------//----------------------//----------------------

int getPreferencesFreeSpace()
{
  return preferencesObject.freeEntries();
}

#endif
