drfailov/DRM_Watch_v3/Firmware/DRM Watch 3/src/MelodyPlayer.h

#ifndef MELODYPLAYER_H
#define MELODYPLAYER_H

/*PROTOTYPPES*/
int melodyPlayerGetLength(const int* melody);
bool melodyPlayerProcessButtons(bool alarm);
void melodyPlayerDrawScreen(bool alarm);
const char* getMelodyNameC(int index);
String getMelodyName(int index);
int getMelodyCount();
void melodyPlayerSetMelodyName(String _name);
bool melodyPlayerPlayMelody(const int* melody, bool alarm);
const int* getMelodyData(int index);

#include "Lcd.h"
#include "Led.h"
#include "Backlight.h"
#include "Buzzer.h"
#include "Button.h"
#include "Icons.h"
#include "AutoSleep.h"
#include "ModeTimer.h"
#include "ModeWatchface.h"


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
, -167, 784, -333, 659, -167, 523, -167, 392, -167, 440, -333, 523, -333, 659, -167, 587, -333, 523, -1000, 1319, -167, 1397, -167, 1480, -167, 1568, -333, 1760, -167, 1568, -333, 1319, -167, 1397, -167, 1480, -167, 1568, -333, 1760, -167, 1568, -333, 1319, -167, 1047, -167, 784, -167, 880, -167, 988, -167, 1047, -167, 1175, -167, 1319, -167, 1175, -167, 1047, -167, 1175, -167, 784, -167, 1319, -167, 1397, -167, 1568, -167, 1760, -167, 1568, -167, 1319, -167, 1397, -167, 1568, -333, 1760, -167, 1568, -333, 1047, -167, 1397, -167, 1480, -167, 1568, -333, 1760, -167, 1568, -333, 1568, -167, 1760, -167, 19};
const int stillalive[]={784, -250, 740, -250, 659, -250, 659, -250, 740, -250, -2500, 440, -250, 784, -250, 740, -250, 659, -250, 659, -500, 740, -250, -500, 587, -500, 659, -250, 440, -500, -1500, 440, -250, 659, -500, 740, -250, 784, -750, 659, -250, 554, -500, 587, -750, 659, -500, 440, -250, 440, -500, 740, -500, -2250, 784, -250, 740, -250, 659, -250, 659, -250, 740, -250, -2500, 440, -250, 784, -250, 740, -250, 659, -250, 659, -500, -250, 740, -250, 587, -500, -250, 659, -250, 440, -500, -1750, 659, -500, 740, -250, 784, -750, 659, -250, 554, -750, 587, -250, 659, -250, -250, 440, -250, 587, -250, 659, -250, 698, -250, 659, -250, 587, -250, 523, -250, -500, 440, -250, 466, -250, 523, -500, 698, -500, 659, -250, 587, -250, 587, -250, 523, -250, 587, -250, 523, -250, 523, -500, 523, -250, -250, 440, -250, 466, -250, 523, -500, 698, -500, 784, -250, 698, -250, 659, -250, 587, -250, 587, -250, 659, -250, 698, -500, 698, -250, -250, 784, -250, 880, -250, 932, -250, 932, -250, 880, -500, 784, -500, 698, -250, 784, -250, 880, -250, 880, -250, 784, -500, 698, -500, 587, -250, 523, -250, 587, -250, 698, -250, 698, -250, 659, -500, 659, -250, 740, -250, 740, -1000, -6000, 440, -250, 784, -250, 740, -250, 659, -250, 659, -250, 740, -250, -2750, 784, -250, 740, -250, 659, -250, 659, -750, 740, -250, 587, -500, 659, -500, 440, -500, -1750, 659, -500, 740, -250, 784, -750, 659, -500, 554, -500, 587, -250, 659, -750, 440, -250, 440, -500, 740, -500, -2000, 440, -250, 587, -250, 784, -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
const int tetris[]={330, -375, 247, -188, 262, -188, 294, -375, 262, -188, 247, -188, 220, -375, 220, -188, 262, -188, 330, -375, 294, -188, 262, -188, 247, -375, 247, -94, 247, -94, 262, -188, 294, -375, 330, -375, 262, -375, 220, -375, 220, -375, -563, 294, -375, 349, -188, 440, -375, 392, -188, 349, -188, 330, -375, -188, 262, -188, 330, -375, 294, -188, 262, -188, 247, -375, 247, -188, 262, -188, 294, -375, 330, -375, 262, -375, 220, -375, 220, -375, 19};
//----------------------//----------------------//----------------------//----------------------//----------------------//----------------------//----------------------



struct Melody {             
  String name;   
  const int* data;         
  Melody(String _name, const int* _data):name(_name), data(_data) {}
  Melody(String _name, const byte* _data):name(_name), data((const int*)_data) {}
};    

Melody melodies[]={   //відсортовано по алфавіту
  {"Alert Timer 1", alert1},
  {"Alert Timer 2", alert2},
  {"Angry Birds", angrybirds},
  {"Astronomia", astronomia},
  {"Badinerie", badinerie},
  {"Believer", believer},
  {"Benny Hill", bennyhill},
  {"Better Off Alone", BetterOffAlone},
  {"Blinding Lights", blindinglights},
  {"Blue", blue},
  {"Chiquitita", chiquitita},
  {"Crab Rave", crabrave},
  {"Crazy Frog", crazyfrog},
  {"Dog Waltz", dogwaltz},
  {"Entertainer", entertainer},
  {"Espionage", espionage},
  {"Funkytown", funkytown},
  {"Gandalf Sax", gandalfsong},
  {"Game Of Thrones", GameOfThrones},
  {"Groovy Blue", groovyBlue},
  {"GTA", gta},
  {"Harry Potter", harrypotter},
  {"Imperial March", imperialmarch},
  {"Jingle Bells", jinglebells},
  {"Jojo", jojo},
  {"Maxwell The Cat", maxwell},
  {"Mealovania", megalovania},
  {"Mission Impossible", missionimpossible},
  {"My Little Pony", mylittlepony},
  {"Newer Gonna Give You Up", newergonnagiveyouup},  
  {"Nokia Tune", nokiaTune},  
  {"Nyan Cat", nyancat},
  {"Popcorn", popcorn},
  {"Roll On", rollon},
  {"Shape of my heart", shapeofmyheart},
  {"Sobak", sobak},
  {"Sleigh Ride", sleighride},
  {"Stereo Love", stereoLove},
  {"Still Alive", stillalive},
  {"Swimming", swimming},
  {"Tetris", tetris},
  {"Toreador", toreador},
  {"Trance", trance},
  {"X-Files", xfiles},
  {"Was Woller Wir Trinken", wasWollenWirTrinken},
  {"Гімн України", ukraine},
  {"Koзaцький Mapш", cossacmarch},
  {"Mapio", mario},
  {"На свою голову", nasvoyugolovu},
  {"Польська Корівка", polskakorivka},
  {"Щедрик", carol}
};

int getMelodyCount()
{
   return sizeof(melodies)/sizeof(melodies[0]);
}

const char* getMelodyNameC(int index)
{
   return melodies[index].name.c_str();
}
String getMelodyName(int index)
{
   return melodies[index].name;
}

const int* getMelodyData(int index)
{
   return melodies[index].data;
}





bool melodyPlayerLoopMelody = false;   
String melodyPlayerMelodyName;
unsigned long melodyPlayerPlayStarted = 0;

void melodyPlayerSetMelodyName(String _name)
{
  melodyPlayerMelodyName=_name;
}
//return true if was played completely or false if interrupted
bool melodyPlayerPlayMelody(const int* melody, bool alarm) 
{
  Serial.println(F("Open: PlayMelody"));
  clearScreenAnimation();
  while(isButtonCenterPressed()); 
  backlightOn();
  melodyPlayerPlayStarted = millis();
  //modeLoop = melodyPlayerDrawScreen;
  //modeButtonUp = 0;
  //modeButtonCenter = 0;
  //modeButtonDown = 0;
  //modeButtonUpLong = 0;
  //modeButtonCenterLong = 0;
  //modeButtonDownLong = 0;
  //enableAutoReturn = false;
  //melodyPlayerLoopMelody = false;
  
  int length = melodyPlayerGetLength(melody);
  Serial.print("length="); Serial.println(length);
  int prequencyThreshold = 0;
  {//analyze melody
    long noteSum = 0;
    long noteCnt = 0;
    for (int i = 1; i < length-1; i++) {
      int n = (melody[i]);
      if (n > 0){
        noteSum += n;
        noteCnt ++;
      }
    }
    if(noteCnt == 0)
      return true;
    prequencyThreshold = 100 + noteSum/noteCnt;
    Serial.print("frequencyThreshold="); Serial.println(prequencyThreshold);
  }
  do{
    melodyPlayerDrawScreen(alarm);
    for (int i = 0; i < length-1; i++) {
      int note = (melody[i]);
      if(note > 0){ //it's frequency
        if(note > 10 && note < 20000)
          buzTone(note);
        if(note>prequencyThreshold)
          ledFlashlightOnBottom();
        else
          ledFlashlightOnTop();
      }
      if(note < 0){ //it's time
        for(unsigned long noteStarted = millis(); millis() - noteStarted < (-note); ) {
          if((millis() - noteStarted)+150 < (-note)){
            if(melodyPlayerProcessButtons(alarm)) 
              return false; //false = melody interrupted
            melodyPlayerDrawScreen(alarm);
          }
        }
        if(melodyPlayerProcessButtons(alarm)) 
          return false; //false = melody interrupted
        ledFlashlightOffAll();
        buzNoTone();
      }  
    }
    delay(500);
  }while(melodyPlayerLoopMelody);
  //if(!alarm) modeSetup();
  return true;
}

//returns true if user stopped playing
bool melodyPlayerProcessButtons(bool alarm){
  if(isButtonCenterPressed())
  {
    buttonBeep(); 
    //modeSetup(); 
    registerAction(); //to brevent auto exit after melody played
    clearScreenAnimation();
    ledFlashlightOffAll(); 
    while(isButtonCenterPressed()); 
    return true;
  }
  if(alarm){
    if(!isTimerRunning())
    {  
      if(isButtonUpPressed())
      {
        buttonBeep(); 
        //modeSetup(); 
        registerAction(); //to brevent auto exit after melody played
        clearScreenAnimation();
        setTimerToMinutes(10); 
        drawMessageAnimated(L("Відкладено на 10 хвилин", "Delayed for 10 minutes"));  
        ledFlashlightOffAll(); 
        buzNoTone();
        while(isButtonUpPressed()); 
        return true;
      }
      if(isButtonDownPressed())
      {
        buttonBeep(); 
        //modeSetup(); 
        registerAction(); //to brevent auto exit after melody played
        clearScreenAnimation();
        setTimerToMinutes(5); 
        drawMessageAnimated(L("Відкладено на 5 хвилин", "Delayed for 5 minutes"));  
        ledFlashlightOffAll(); 
        buzNoTone();
        while(isButtonDownPressed()); 
        return true;
      }
    }
  }
  else{
    if(isButtonDownPressed())
    {
      buttonBeep(); 
      registerAction(); //to brevent auto exit after melody played
      melodyPlayerLoopMelody = !melodyPlayerLoopMelody; 
      drawMessageAnimated(melodyPlayerLoopMelody?L("Повтор увімкнено", "Repeat ON"):L("Вимкнено повтор","Repeat OFF"));  
      while(isButtonDownPressed()); 
    }
  }
  return false;
}

void melodyPlayerDrawScreen(bool alarm) {

  lcd()->setColorIndex(white);
  lcd()->drawBox(0, 0, 400, 240);

  lcd()->setFont(u8g2_font_10x20_t_cyrillic);  //ok
  lcd()->setCursor(5, 18); 
  lcd()->setColorIndex(black);
  if(alarm)
    lcd()->print(L("Сповіщення", "Alert"));
  else
    lcd()->print(L("Плеєр", "Player"));
  
  int x = drawStatusbar(363, 1, true); 
  if(melodyPlayerLoopMelody)      //draw repeat icon next to statusbar
    draw_ic16_repeat(x-16, 5, black);
  

  displayDrawVector(getPathZubat(), 130, 45, 3.0, 3, false, black);
  
  lcd()->setFont(u8g2_font_10x20_t_cyrillic);  //ok
  lcd()->setCursor(5, 230); 
  int sec = (millis()-melodyPlayerPlayStarted)/1000;
  if(sec < 10)
    lcd()->print("0");
  lcd()->print(sec);
  lcd()->print("s");

  drawCentered(melodyPlayerMelodyName, 200);

  lcd()->drawBox(369, 0, 2, 260);  //draw_ic16_repeat  draw_ic16_arrow_right  draw_ic16_back
  if(alarm){
    draw_ic16_back(lx(), ly2(), black);
    if(!isTimerRunning()){  
      lcd()->setFont(u8g2_font_unifont_t_cyrillic); //smalll 
      lcd()->setCursor(lx()-5, ly1()+16); lcd()->print("+10");
      lcd()->setCursor(lx()-1, ly3()+16); lcd()->print("+5");
    }
  }
  else{
    draw_ic16_back(lx(), ly2(), black);
    draw_ic16_repeat(lx(), ly3(), black);
  }
  lcd()->sendBuffer();
}

void printBits(byte myByte) {
  for (byte mask = 0x80; mask; mask >>= 1) {
    if (mask & myByte)
      Serial.print('1');
    else
      Serial.print('0');
  }
}

int melodyPlayerGetLength(const int* melody) {
  for (int i = 0; i < 5000; i++) {
    //Serial.print("i="); Serial.println(i);
    int b = (melody[i]);
    if (b == 19) { //EOF
      return i + 1;
    }
  }
  return 5000;
}

















#endif
