drfailov/DRM_Watch_v3/Firmware/DRM Watch 3/src/Icons.h

#ifndef ICONS_H
#define ICONS_H

#include "Lcd.h"

int lx(){return 378;}
int ly1(){return 50;}
int ly2(){return 120;}
int ly3(){return 185;}
void draw_ic32_empty(int x, int y, bool color){lcd()->setColorIndex(!color); lcd()->drawBox(x, y, 32, 32);}
void draw_ic24_empty(int x, int y, bool color){lcd()->setColorIndex(!color); lcd()->drawBox(x, y, 24, 24);}
void draw_ic16_empty(int x, int y, bool color){lcd()->setColorIndex(!color); lcd()->drawBox(x, y, 16, 16);}



//------------------------------------------------------------------------------
// File generated by LCD Assistant
// http://en.radzio.dxp.pl/bitmap_converter/
//------------------------------------------------------------------------------

const unsigned char ic16_check [] = {
0x00, 0x00, 0x00, 0x00, 0x00, 0x0E, 0x00, 0x1F, 0x00, 0x3F, 0x00, 0x7E, 0x60, 0xFC, 0xF1, 0xF8,
0xFB, 0xF0, 0xFF, 0xE0, 0x7F, 0xC0, 0x3F, 0x80, 0x1F, 0x00, 0x0E, 0x00, 0x00, 0x00, 0x00, 0x00
};void draw_ic16_check(int x, int y, bool color){lcd()->setColorIndex(color);  lcd()->drawBitmap(x, y, 2, 16, ic16_check);}


const unsigned char ic16_backspace [] = {
0x00, 0x00, 0x00, 0x00, 0x07, 0xFE, 0x0F, 0xFF, 0x1F, 0xFF, 0x3C, 0xE7, 0x7E, 0x4F, 0xFF, 0x1F,
0x7E, 0x4F, 0x3C, 0xE7, 0x1F, 0xFF, 0x0F, 0xFF, 0x07, 0xFE, 0x00, 0x00, 0x00, 0x00, 0x00, 0x00
};void draw_ic16_backspace(int x, int y, bool color){lcd()->setColorIndex(color);  lcd()->drawBitmap(x, y, 2, 16, ic16_backspace);}


const unsigned char ic16_shift_normal [] = {
0x01, 0x80, 0x03, 0xC0, 0x07, 0xE0, 0x0F, 0xF0, 0x1F, 0xF8, 0x3F, 0xFC, 0x7F, 0xFE, 0xFF, 0xFF,
0x0F, 0xF0, 0x0F, 0xF0, 0x0F, 0xF0, 0x0F, 0xF0, 0x0F, 0xF0, 0x0F, 0xF0, 0x0F, 0xF0, 0x0F, 0xF0
};void draw_ic16_shift_normal(int x, int y, bool color){lcd()->setColorIndex(color);  lcd()->drawBitmap(x, y, 2, 16, ic16_shift_normal);}


const unsigned char ic16_shift_cap [] = {
0x01, 0x80, 0x03, 0xC0, 0x07, 0xE0, 0x0F, 0xF0, 0x1F, 0xF8, 0x3F, 0xFC, 0x7F, 0xFE, 0xFF, 0xFF,
0x0F, 0xF0, 0x0F, 0xF0, 0x0F, 0xF0, 0x0F, 0xF0, 0x0F, 0xF0, 0x0F, 0xF0, 0x00, 0x00, 0x0F, 0xF0
};void draw_ic16_shift_cap(int x, int y, bool color){lcd()->setColorIndex(color);  lcd()->drawBitmap(x, y, 2, 16, ic16_shift_cap);}


const unsigned char ic16_shift_sym [] = {
0x01, 0x80, 0x03, 0xC0, 0x07, 0xE0, 0x0F, 0xF0, 0x1F, 0xF8, 0x3F, 0xFC, 0x7F, 0xFE, 0xFF, 0xFF,
0x0F, 0xF0, 0x0F, 0xF0, 0x0F, 0xF0, 0x0F, 0xF0, 0x00, 0x00, 0x0F, 0xF0, 0x00, 0x00, 0x0F, 0xF0
};void draw_ic16_shift_sym(int x, int y, bool color){lcd()->setColorIndex(color);  lcd()->drawBitmap(x, y, 2, 16, ic16_shift_sym);}


const unsigned char ic16_cancel [] = {
0x60, 0x06, 0xF0, 0x0F, 0xF8, 0x1F, 0x7C, 0x3E, 0x3E, 0x7C, 0x1F, 0xF8, 0x0F, 0xF0, 0x07, 0xE0,
0x07, 0xE0, 0x0F, 0xF0, 0x1F, 0xF8, 0x3E, 0x7C, 0x7C, 0x3E, 0xF8, 0x1F, 0xF0, 0x0F, 0x60, 0x06
};void draw_ic16_cancel(int x, int y, bool color){lcd()->setColorIndex(color);  lcd()->drawBitmap(x, y, 2, 16, ic16_cancel);}


const unsigned char ic16_coffee [] = {
0x00, 0x00, 0xFF, 0xF8, 0xBF, 0xFF, 0xBF, 0xF9, 0xBF, 0xF9, 0xBF, 0xFB, 0xBF, 0xFE, 0xDF, 0xF8,
0x5F, 0xF0, 0x7F, 0xF0, 0x3F, 0xE0, 0x1F, 0xC0, 0x00, 0x00, 0xFF, 0xFC, 0x7F, 0xF8, 0x00, 0x00
};void draw_ic16_coffee(int x, int y, bool color){lcd()->setColorIndex(color);  lcd()->drawBitmap(x, y, 2, 16, ic16_coffee);}


const unsigned char ic16_arrow_up [] = {
0x00, 0x00, 0x00, 0x00, 0x00, 0x00, 0x01, 0x80, 0x03, 0xC0, 0x07, 0xE0, 0x0F, 0xF0, 0x1F, 0xF8,
0x3F, 0xFC, 0x7F, 0xFE, 0xFF, 0xFF, 0xFF, 0xFF, 0x00, 0x00, 0x00, 0x00, 0x00, 0x00, 0x00, 0x00
};void draw_ic16_arrow_up(int x, int y, bool color){lcd()->setColorIndex(color);  lcd()->drawBitmap(x, y, 2, 16, ic16_arrow_up);}


const unsigned char ic16_arrow_down [] = {
0x00, 0x00, 0x00, 0x00, 0x00, 0x00, 0x00, 0x00, 0xFF, 0xFF, 0xFF, 0xFF, 0x7F, 0xFE, 0x3F, 0xFC,
0x1F, 0xF8, 0x0F, 0xF0, 0x07, 0xE0, 0x03, 0xC0, 0x01, 0x80, 0x00, 0x00, 0x00, 0x00, 0x00, 0x00
};void draw_ic16_arrow_down(int x, int y, bool color){lcd()->setColorIndex(color);  lcd()->drawBitmap(x, y, 2, 16, ic16_arrow_down);}


const unsigned char ic16_flashlight [] = {
0x01, 0x80, 0x01, 0x80, 0x31, 0x8C, 0x38, 0x1C, 0x11, 0x88, 0x07, 0xE0, 0x07, 0xE0, 0xEF, 0xF7,
0xEF, 0xF7, 0x07, 0xE0, 0x07, 0xE0, 0x11, 0x88, 0x38, 0x1C, 0x31, 0x8C, 0x01, 0x80, 0x01, 0x80
};void draw_ic16_flashlight(int x, int y, bool color){lcd()->setColorIndex(color);  lcd()->drawBitmap(x, y, 2, 16, ic16_flashlight);}


const unsigned char ic16_menu [] = {
0x7F, 0xFE, 0xFF, 0xFF, 0x7F, 0xFE, 0x00, 0x00, 0x00, 0x00, 0x00, 0x00, 0x7F, 0xFE, 0xFF, 0xFF,
0x7F, 0xFE, 0x00, 0x00, 0x00, 0x00, 0x00, 0x00, 0x7F, 0xFE, 0xFF, 0xFF, 0x7F, 0xFE, 0x00, 0x00
};void draw_ic16_menu(int x, int y, bool color){lcd()->setColorIndex(color);  lcd()->drawBitmap(x, y, 2, 16, ic16_menu);}


const unsigned char ic16_repeat [] = {
0x00, 0x08, 0x00, 0x0C, 0x1F, 0xFE, 0x3F, 0xFF, 0x7F, 0xFE, 0xF0, 0x0C, 0xE0, 0x08, 0xE0, 0x00,
0x00, 0x07, 0x10, 0x07, 0x30, 0x0F, 0x7F, 0xFE, 0xFF, 0xFC, 0x7F, 0xF8, 0x30, 0x00, 0x10, 0x00
};void draw_ic16_repeat(int x, int y, bool color){lcd()->setColorIndex(color);  lcd()->drawBitmap(x, y, 2, 16, ic16_repeat);}


const unsigned char ic16_arrow_right [] = {
0x0C, 0x00, 0x0E, 0x00, 0x0F, 0x00, 0x0F, 0x80, 0x0F, 0xC0, 0x0F, 0xE0, 0x0F, 0xF0, 0x0F, 0xF8,
0x0F, 0xF8, 0x0F, 0xF0, 0x0F, 0xE0, 0x0F, 0xC0, 0x0F, 0x80, 0x0F, 0x00, 0x0E, 0x00, 0x0C, 0x00
};void draw_ic16_arrow_right(int x, int y, bool color){lcd()->setColorIndex(color);  lcd()->drawBitmap(x, y, 2, 16, ic16_arrow_right);} 

const unsigned char ic16_stopwatch [] = {
0x03, 0xC0, 0x01, 0x80, 0x07, 0xE6, 0x1F, 0xFE, 0x3C, 0x3C, 0x30, 0xCC, 0x70, 0xEE, 0x60, 0xF6,
0x60, 0xF6, 0x60, 0x06, 0x60, 0x06, 0x70, 0x0E, 0x30, 0x0C, 0x3C, 0x3C, 0x1F, 0xF8, 0x07, 0xE0
};void draw_ic16_stopwatch(int x, int y, bool color){lcd()->setColorIndex(color);  lcd()->drawBitmap(x, y, 2, 16, ic16_stopwatch);}

const unsigned char ic16_back [] = {
0x00, 0x30, 0x00, 0x78, 0x00, 0xF8, 0x01, 0xF0, 0x03, 0xE0, 0x07, 0xC0, 0x0F, 0x80, 0x1F, 0x00,
0x1F, 0x00, 0x0F, 0x80, 0x07, 0xC0, 0x03, 0xE0, 0x01, 0xF0, 0x00, 0xF8, 0x00, 0x78, 0x00, 0x30
};void draw_ic16_back(int x, int y, bool color){lcd()->setColorIndex(color);  lcd()->drawBitmap(x, y, 2, 16, ic16_back);}

const unsigned char ic16_alert [] = {
0x70, 0x0E, 0xF8, 0x1F, 0xF3, 0xCF, 0xEF, 0xF7, 0x5B, 0xFA, 0x1D, 0xF8, 0x3E, 0xFC, 0x3F, 0x7C,
0x3F, 0x7C, 0x3E, 0xFC, 0x3D, 0xFC, 0x3F, 0xFC, 0x1F, 0xF8, 0x1F, 0xF8, 0x33, 0xCC, 0x20, 0x04
};void draw_ic16_alert(int x, int y, bool color){lcd()->setColorIndex(color);  lcd()->drawBitmap(x, y, 2, 16, ic16_alert);}

const unsigned char ic16_plus [] = {
0x01, 0x80, 0x03, 0xC0, 0x03, 0xC0, 0x03, 0xC0, 0x03, 0xC0, 0x03, 0xC0, 0x7F, 0xFE, 0xFF, 0xFF,
0xFF, 0xFF, 0x7F, 0xFE, 0x03, 0xC0, 0x03, 0xC0, 0x03, 0xC0, 0x03, 0xC0, 0x03, 0xC0, 0x01, 0x80
}; void draw_ic16_plus(int x, int y, bool color){lcd()->setColorIndex(color);  lcd()->drawBitmap(x, y, 2, 16, ic16_plus);}

const unsigned char ic16_minus [] = {
0x00, 0x00, 0x00, 0x00, 0x00, 0x00, 0x00, 0x00, 0x00, 0x00, 0x00, 0x00, 0x7F, 0xFE, 0xFF, 0xFF,
0xFF, 0xFF, 0x7F, 0xFE, 0x00, 0x00, 0x00, 0x00, 0x00, 0x00, 0x00, 0x00, 0x00, 0x00, 0x00, 0x00
}; void draw_ic16_minus(int x, int y, bool color){lcd()->setColorIndex(color);  lcd()->drawBitmap(x, y, 2, 16, ic16_minus);}

const unsigned char ic16_sound_mute [] = {
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
  33,  9,    29, 17,    28,  9,    23, 17,    23,  8, //зубы
  20, 16,    23, 23,    27, 15,    29, 23,    33, 15,
  34, 23,   255,255,    31,  2,    31,  4,    31,  3, //глаз
  32,  3,    30,  3
}; const byte* getPathZubat(){return pathZubat;}


#endif
