drfailov/DRM_Watch_v3/Firmware/DRM Watch 3/src/ModeLife.h

#ifndef MODELIFE_H
#define MODELIFE_H

void setModeLife();
void ModeLifeLoop();
void ModeLifeButtonUp();
void ModeLifeButtonCenter();
void ModeLifeButtonDown();
void lifeStep();

#include "Global.h"
#include "AutoSleep.h"
#include "Button.h"
#include "ScreenBuffer.h"
#include "ModeMenuApps.h"
#include "ModeMenuBackgrounds.h"

void setModeLife(){
  clearScreenAnimation();
  Serial.println(F("Set mode: Life"));
  modeSetup = setModeLife;
  modeLoop = ModeLifeLoop;
  modeButtonUp = ModeLifeButtonUp;
  modeButtonCenter = ModeLifeButtonCenter;
  modeButtonDown = ModeLifeButtonDown;
  modeButtonUpLong = 0;
  modeButtonCenterLong = 0;
  modeButtonDownLong = 0;
  registerAction();
  enableAutoReturn = false;
  enableAutoSleep = false; 
  autoReturnTime = autoReturnDefaultTime;
  autoSleepTime = autoSleepDefaultTime;
  randScreenBuffer();
}

void ModeLifeLoop(){ 
  drawScreenBuffer();
  lcd()->sendBuffer();
  unsigned long millisStarted = millis();
  lifeStep();
  unsigned long millisEnd = millis();
  Serial.print("Life step: "); Serial.print(millisEnd-millisStarted); Serial.println("ms.");
}

void ModeLifeButtonUp(){
  setModeBackgroundsMenu();
}

void ModeLifeButtonCenter(){
  setModeBackgroundsMenu();
}

void ModeLifeButtonDown(){
  setModeBackgroundsMenu();
}



void lifeStep(){
  bool lastCol [BUFF_H];
  bool currCol [BUFF_H];
  for(int y = 0; y < BUFF_H; y++)
      currCol[y] = false;
  
  for(int x = 0; x < BUFF_W; x++){
    for(int y = 0; y < BUFF_H; y++)
      lastCol[y] = currCol[y];
    for(int y = 0; y < BUFF_H; y++)
      currCol[y] = getScreenBuffer(x,y);
      
    for(int y = 0; y < BUFF_H; y++){
      //Serial.print(x);Serial.print(", ");Serial.println(y); delay(1);
      bool topleft = y==0?false:lastCol[y-1];
      bool top = y==0?false:currCol[y-1];
      bool topright = y==0?false:getScreenBuffer(x + 1, y-1);
      
      bool left = lastCol[y];
      bool current = currCol[y];
      bool right = x>=BUFF_W-1?false:getScreenBuffer(x + 1, y);
      
      bool bottomleft = y>=BUFF_H-1?false:lastCol[y+1];
      bool bottom = y>=BUFF_H-1?false:currCol[y+1];
      bool bottomright = y>=BUFF_H-1?false:(x>=BUFF_W-1?false:getScreenBuffer(x+1, y+1)); //============todo

      int neighbours = topleft+top+topright+left+right+bottomleft+bottom+bottomright;
      
      bool c;
      if(current)
        c = (neighbours == 2 || neighbours == 3);
      else
        c = neighbours == 3;
      setScreenBuffer(x, y, c);
    }
  }
}






#endif
