drfailov/DRM_Watch_v3/Firmware/DRM Watch 3/src/SettingsMenu/ModeWiFiScanner.h

#ifndef MODEWIFISCANNER_H
#define MODEWIFISCANNER_H

/*PROTOTYPES*/
void setModeWiFiScanner(Runnable onSelected, Runnable onCancel);
void setModeWiFiScanner();
void setModeWiFiScanner_();
void modeWiFiScannerLoop();
void modeWiFiScannerButtonCenter();
void wifiOff();
const char* encryprionType(int i);
String modeWiFiScannerGetSelectedNetworkName();
bool tryConnectWifi(String ssid, String password, Runnable onConnected, Runnable onFailed);

#include "../Global.h"
#include "../AutoSleep.h"
#include "../Button.h"
#include "../GlobalMenu.h"
#include "ModeSavedWiFiList.h"

#include <WiFi.h>

String modeWiFiScannerSelectedNetwork = "";
Runnable modeWiFiScannerOnNetworkSelected = 0;
Runnable modeWiFiScannerOnCancel = 0;

const int modeWiFiScannerStatePreparing = 0;
const int modeWiFiScannerStateSettingUp = 1;
const int modeWiFiScannerStateSettingUpDelay = 2;
const int modeWiFiScannerStateSettingUpScanning = 3;
const int modeWiFiScannerStateSettingUpNoNetworks = 4;
const int modeWiFiScannerStateSettingUpSelectingNetwork = 5;
int modeWiFiScannerState = 0;
long modeWiFiScannerStateChangeTime = 0;

void setModeWiFiScanner(Runnable onSelected, Runnable onCancel){
  modeWiFiScannerOnNetworkSelected = onSelected;
  modeWiFiScannerOnCancel = onCancel;
  enableAutoReturn = true;
  setModeWiFiScanner_();
}
void setModeWiFiScanner(){
  setModeWiFiScanner_();
}
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
